jasonsbeer/AmigaPCI/DataSheets/TimingDiagrams/Bus Sizing/ALTERNATING RW BYTE TRANSFER TO LONG WORD PORT.png

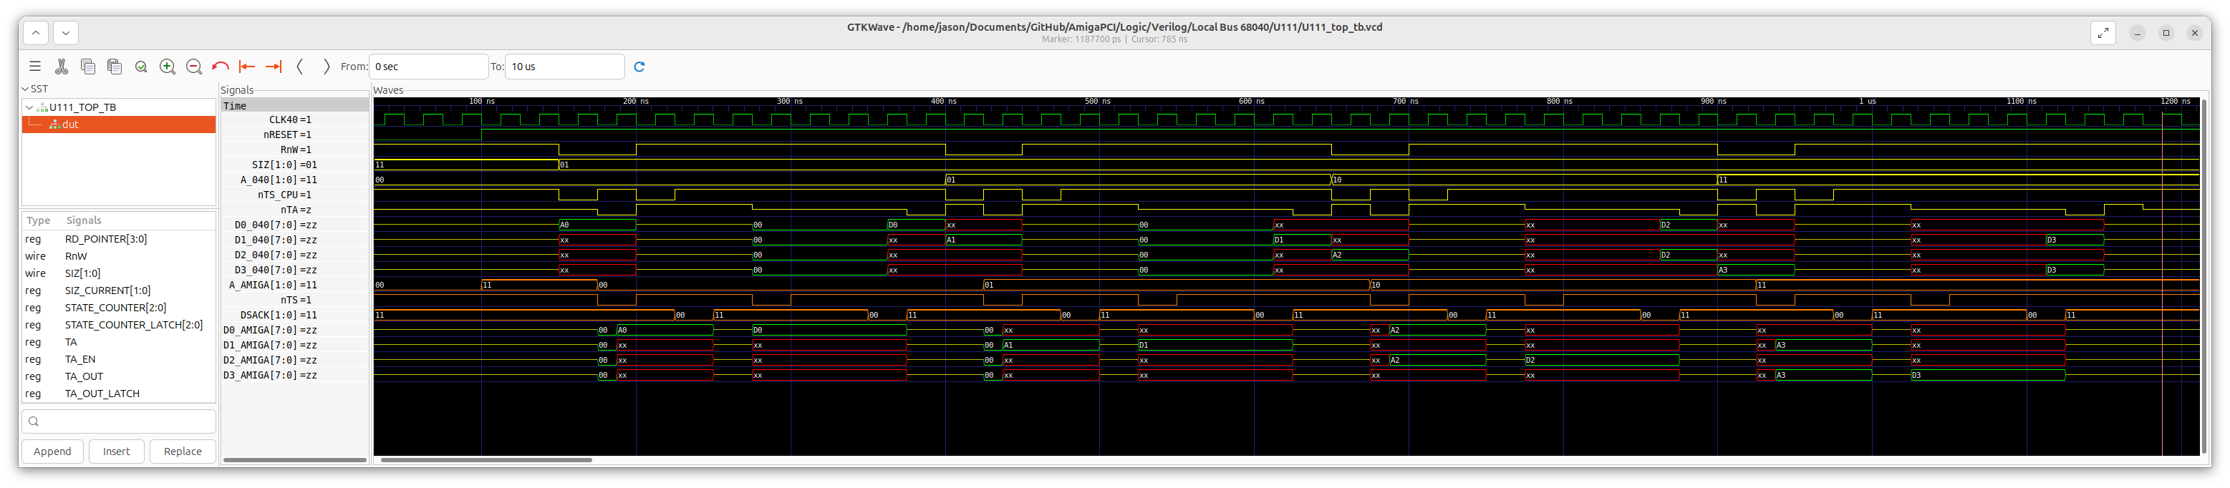
DataSheets/TimingDiagrams/Bus Sizing/ALTERNATING RW BYTE TRANSFER TO LONG WORD PORT.png
