jasonsbeer/AmigaPCI/DataSheets/TimingDiagrams/Bus Sizing/ALTERNATING RW BYTE TRANSFER TO WORD PORT.png

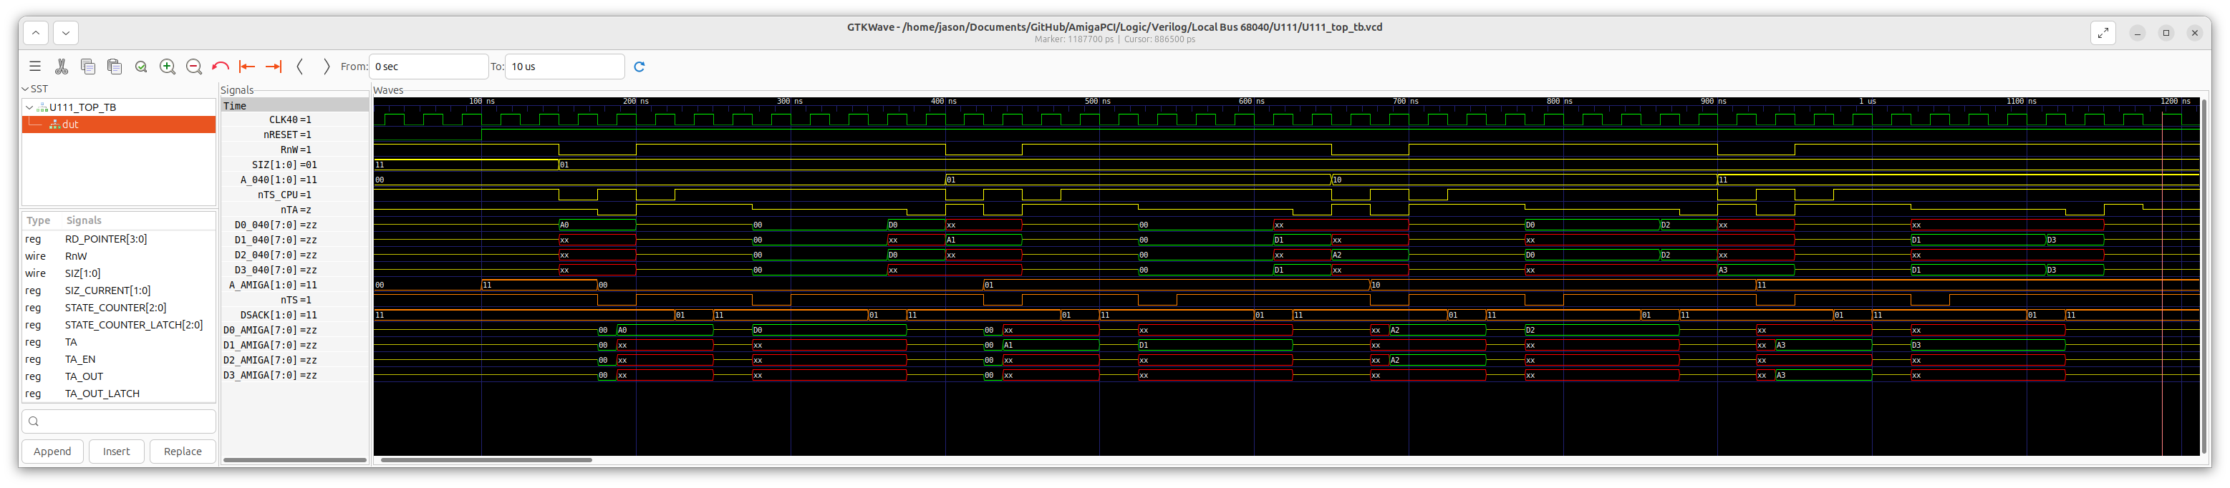
DataSheets/TimingDiagrams/Bus Sizing/ALTERNATING RW BYTE TRANSFER TO WORD PORT.png
