jasonsbeer/AmigaPCI/DataSheets/TimingDiagrams/Bus Sizing/ALTERNATING RW LINE TRANSFER TO LONG WORD PORT WITH WAITS.png

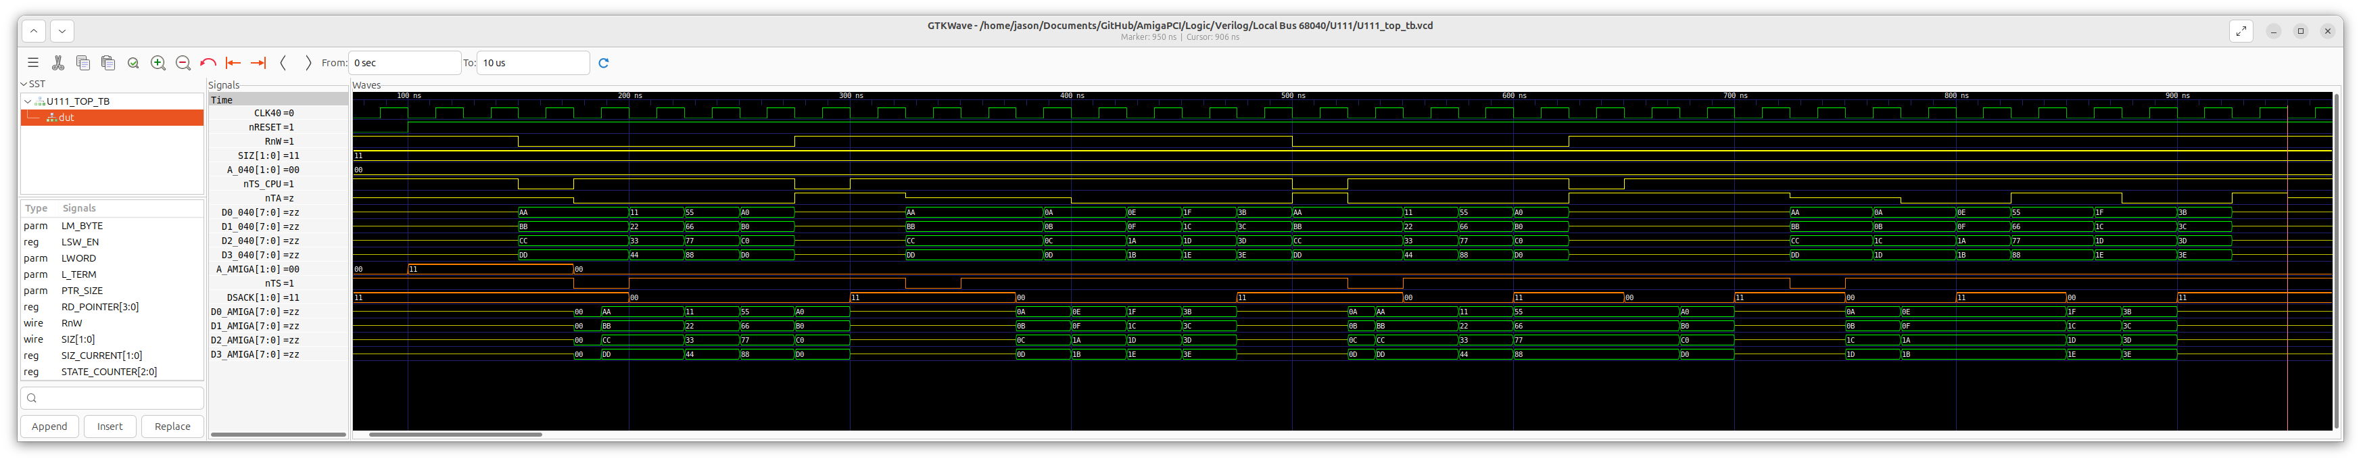
DataSheets/TimingDiagrams/Bus Sizing/ALTERNATING RW LINE TRANSFER TO LONG WORD PORT WITH WAITS.png
