jasonsbeer/AmigaPCI/DataSheets/TimingDiagrams/Bus Sizing/ALTERNATING RW LINE TRANSFER TO WORD PORT.png

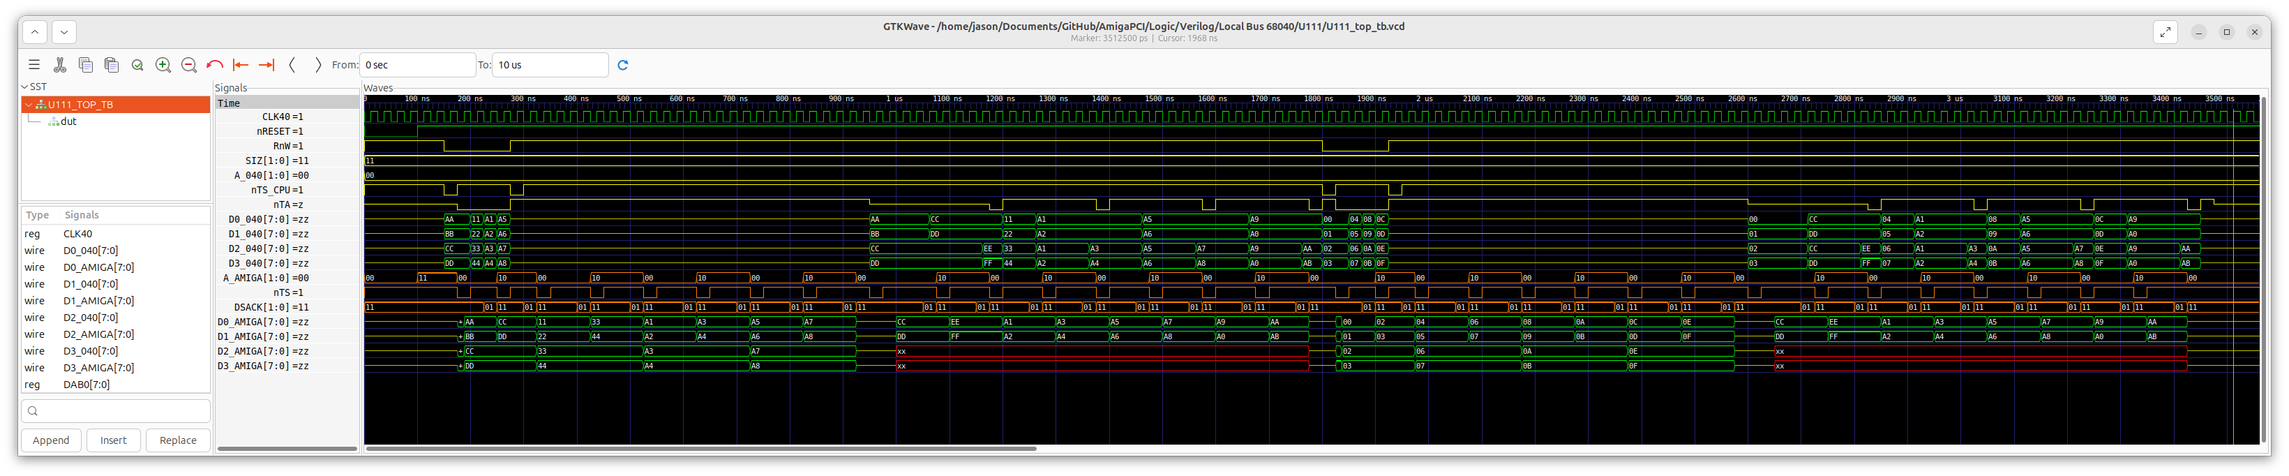
DataSheets/TimingDiagrams/Bus Sizing/ALTERNATING RW LINE TRANSFER TO WORD PORT.png
