jasonsbeer/AmigaPCI/DataSheets/TimingDiagrams/Bus Sizing/ALTERNATING RW LONG WORD TO WORD PORT.png

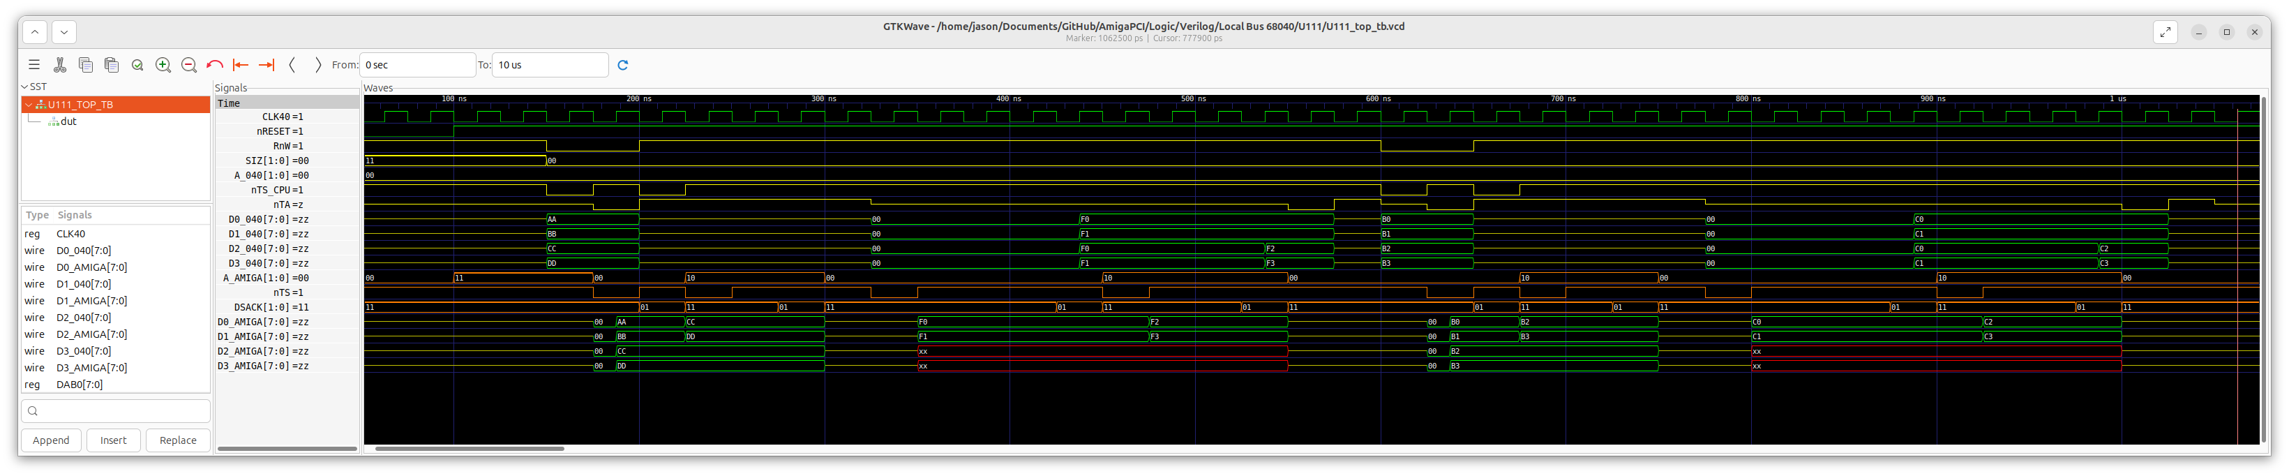
DataSheets/TimingDiagrams/Bus Sizing/ALTERNATING RW LONG WORD TO WORD PORT.png
