jasonsbeer/AmigaPCI/DataSheets/TimingDiagrams/Bus Sizing/ALTERNATING RW WORD TO LONG WORD PORT.png

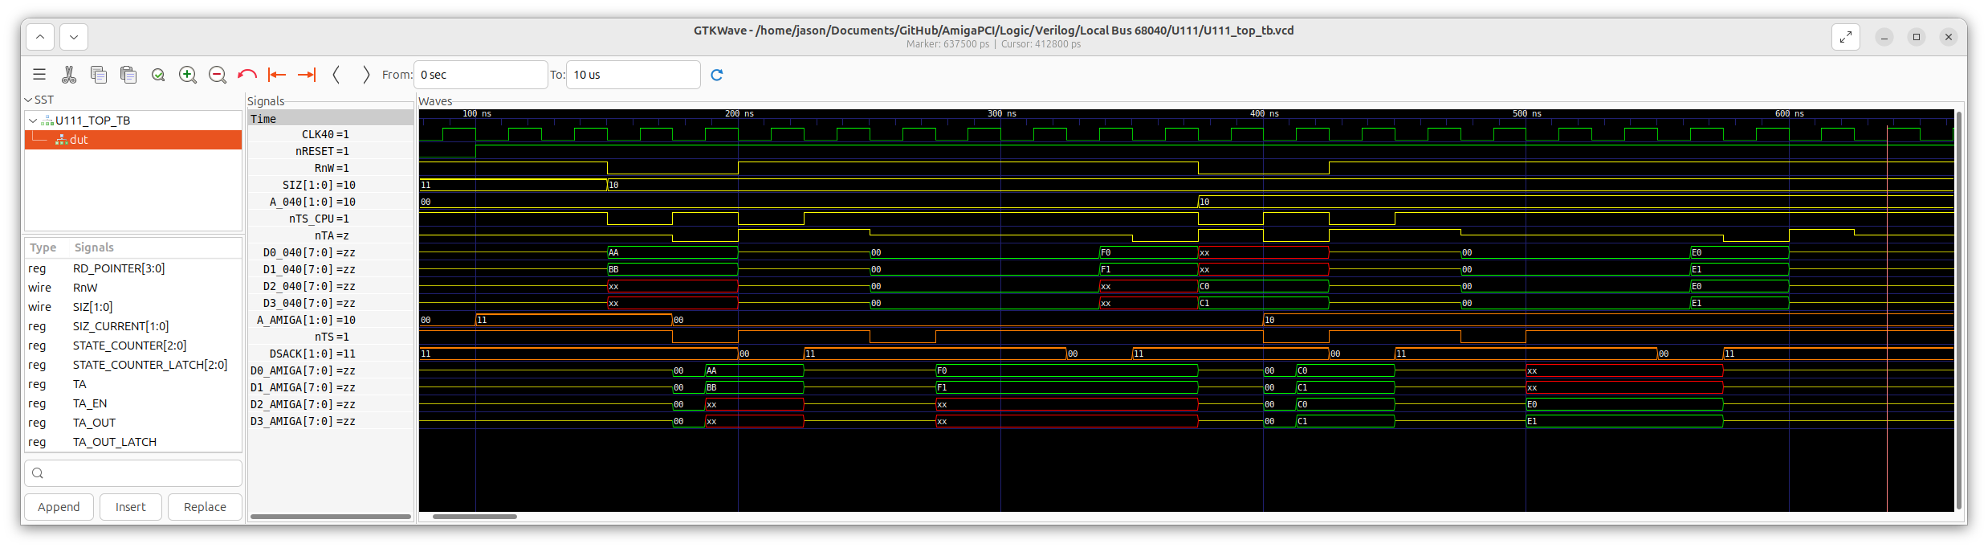
DataSheets/TimingDiagrams/Bus Sizing/ALTERNATING RW WORD TO LONG WORD PORT.png
