jasonsbeer/AmigaPCI/DataSheets/TimingDiagrams/Bus Sizing/BYTE READ FROM LONG WORD PORT.png

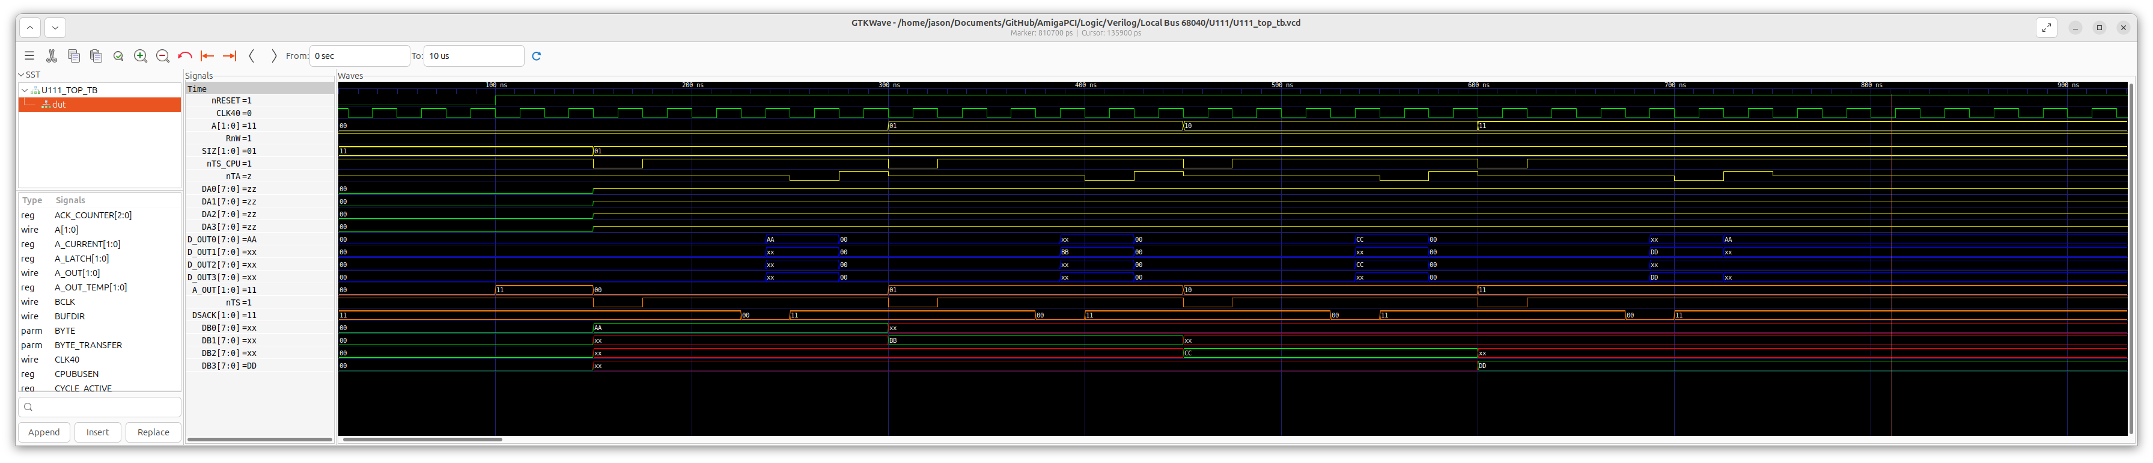
DataSheets/TimingDiagrams/Bus Sizing/BYTE READ FROM LONG WORD PORT.png
