jasonsbeer/AmigaPCI/DataSheets/TimingDiagrams/Bus Sizing/BYTE READ FROM WORD PORT.png

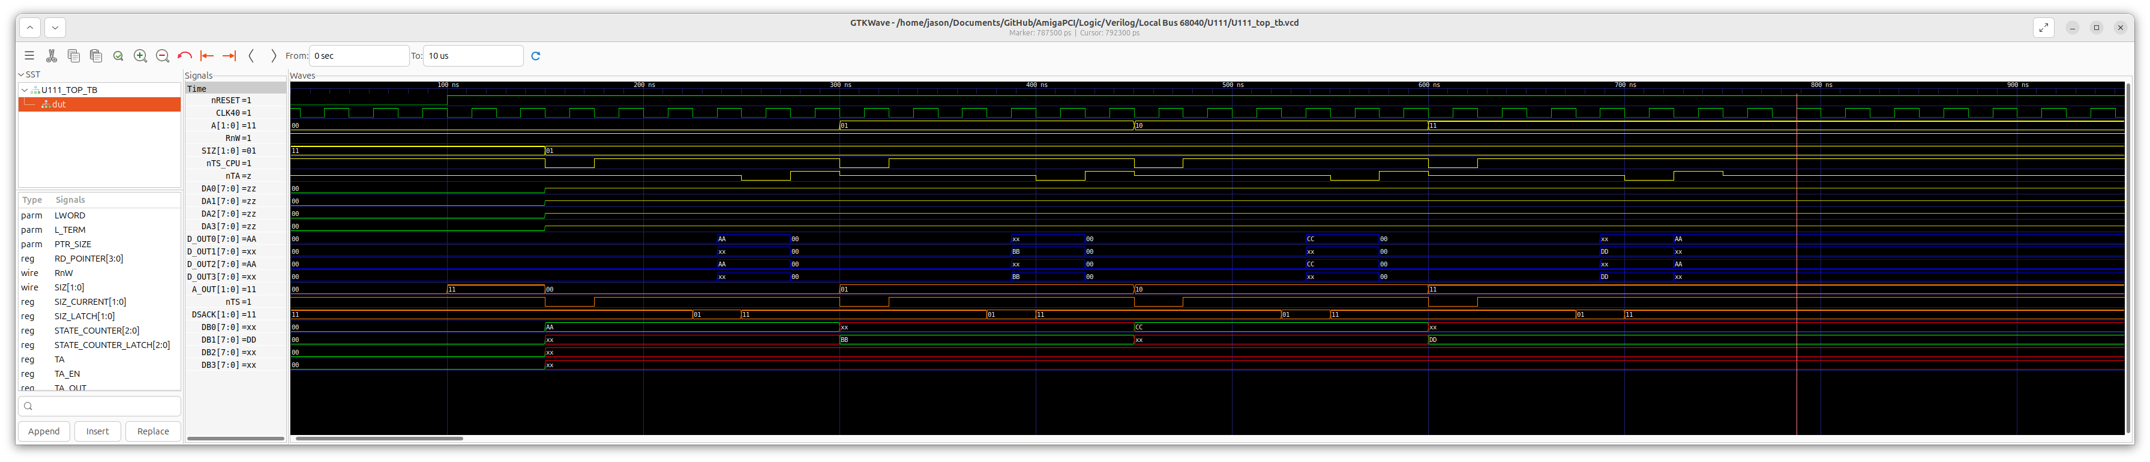
DataSheets/TimingDiagrams/Bus Sizing/BYTE READ FROM WORD PORT.png
