jasonsbeer/AmigaPCI/DataSheets/TimingDiagrams/Bus Sizing/BYTE WRITE TO LONG WORD PORT.png

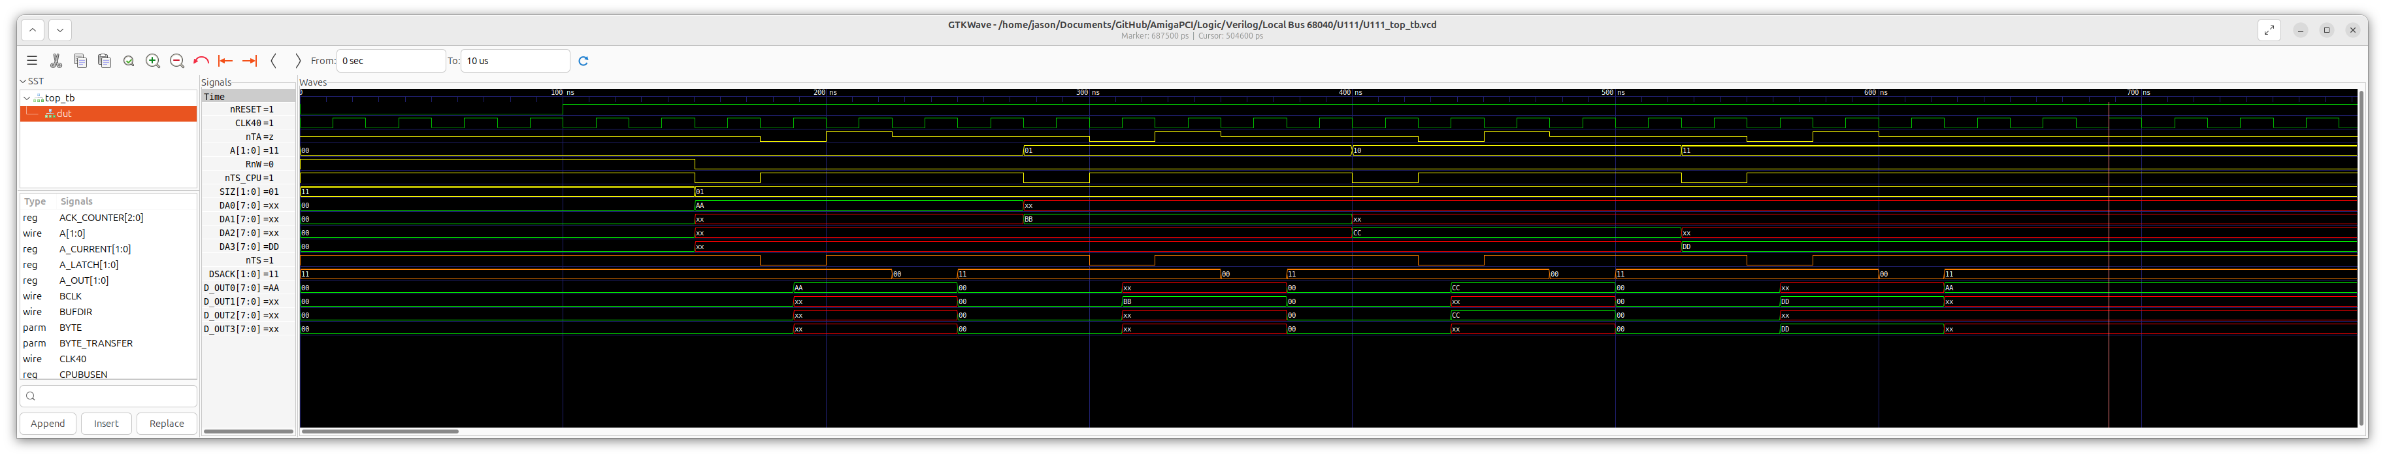
DataSheets/TimingDiagrams/Bus Sizing/BYTE WRITE TO LONG WORD PORT.png
