jasonsbeer/AmigaPCI/DataSheets/TimingDiagrams/Bus Sizing/LINE READ FROM A WORD PORT.png

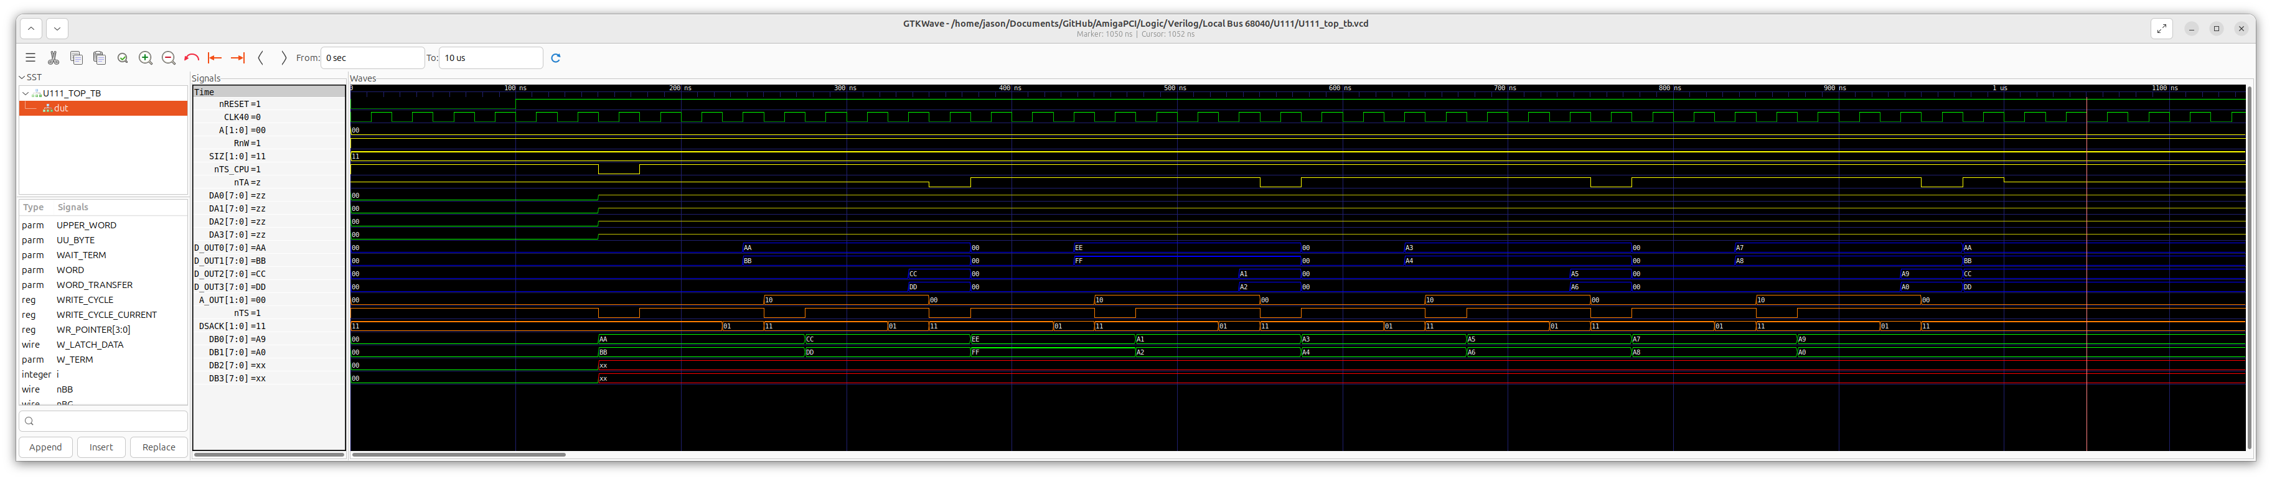
DataSheets/TimingDiagrams/Bus Sizing/LINE READ FROM A WORD PORT.png
