jasonsbeer/AmigaPCI/DataSheets/TimingDiagrams/Bus Sizing/LINE READ FROM LONG WORD PORT.png

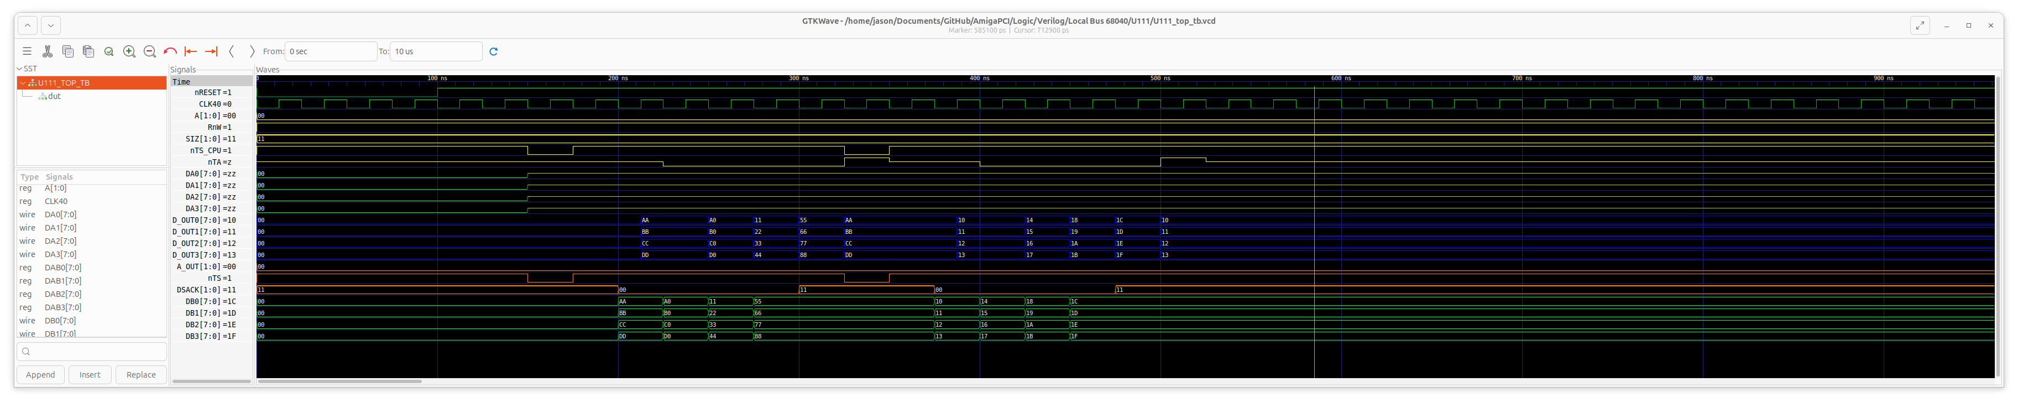
DataSheets/TimingDiagrams/Bus Sizing/LINE READ FROM LONG WORD PORT.png
