jasonsbeer/AmigaPCI/DataSheets/TimingDiagrams/Bus Sizing/LINE WRITE TO LONG WORD PORT.png

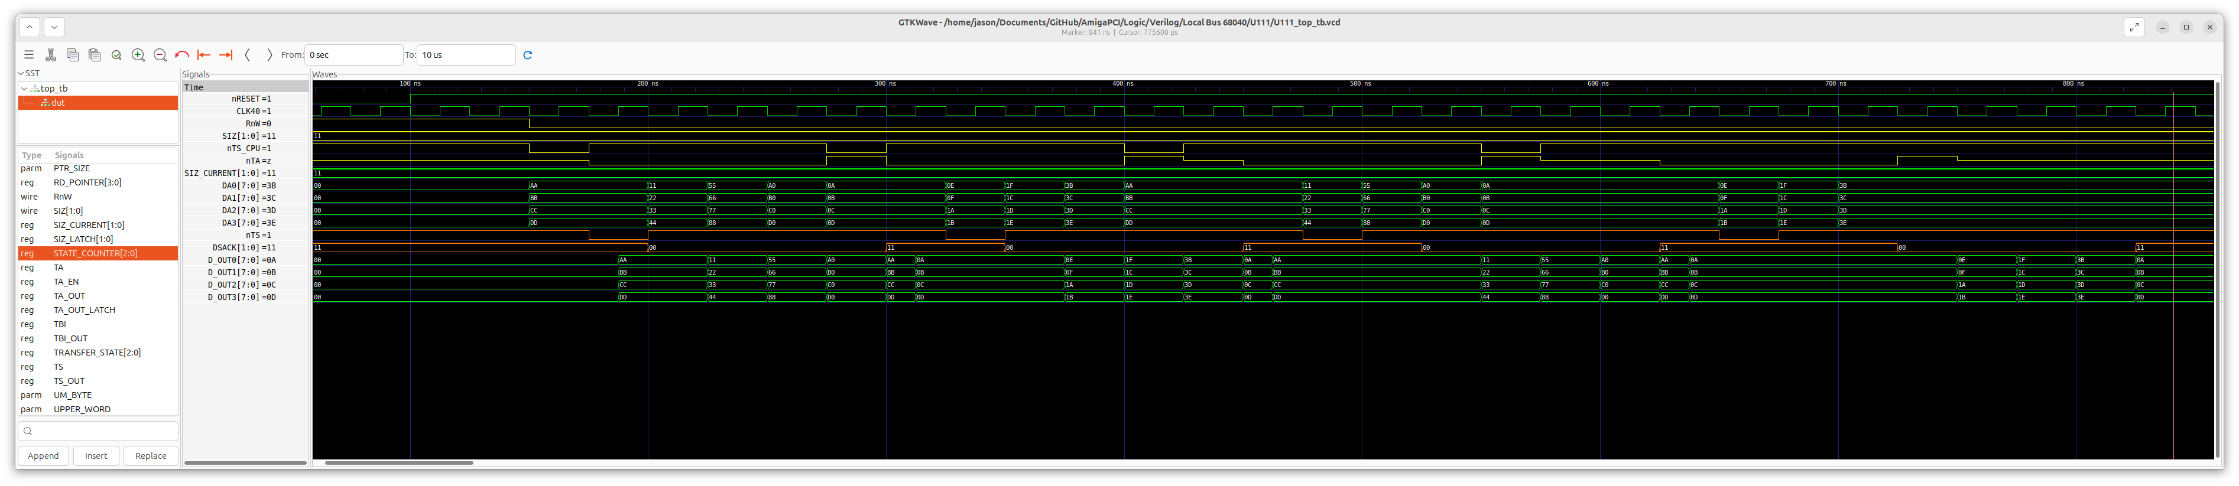
DataSheets/TimingDiagrams/Bus Sizing/LINE WRITE TO LONG WORD PORT.png
