jasonsbeer/AmigaPCI/DataSheets/TimingDiagrams/Bus Sizing/LINE WRITE TO WORD PORT.png

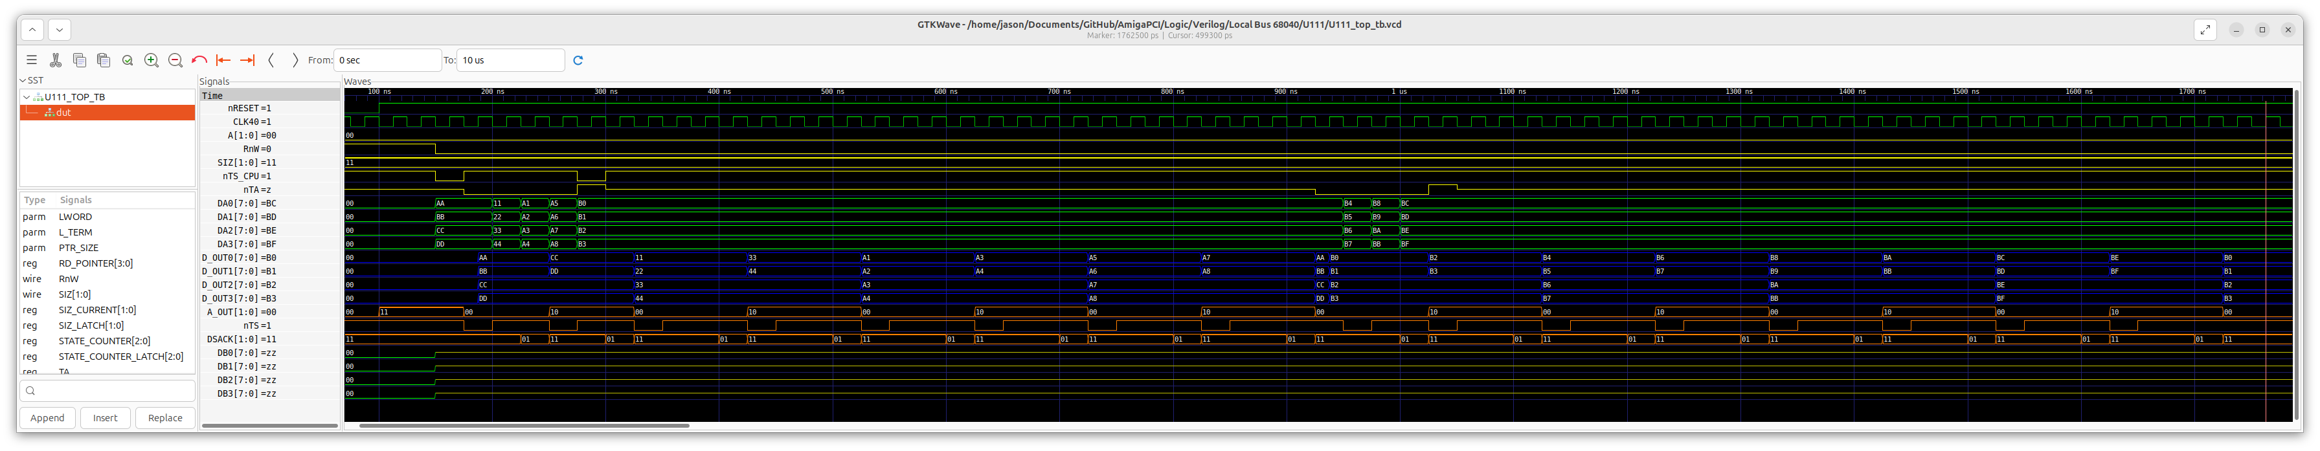
DataSheets/TimingDiagrams/Bus Sizing/LINE WRITE TO WORD PORT.png
