jasonsbeer/AmigaPCI/DataSheets/TimingDiagrams/Bus Sizing/LONG WORD READ FROM LONG WORD PORT.png

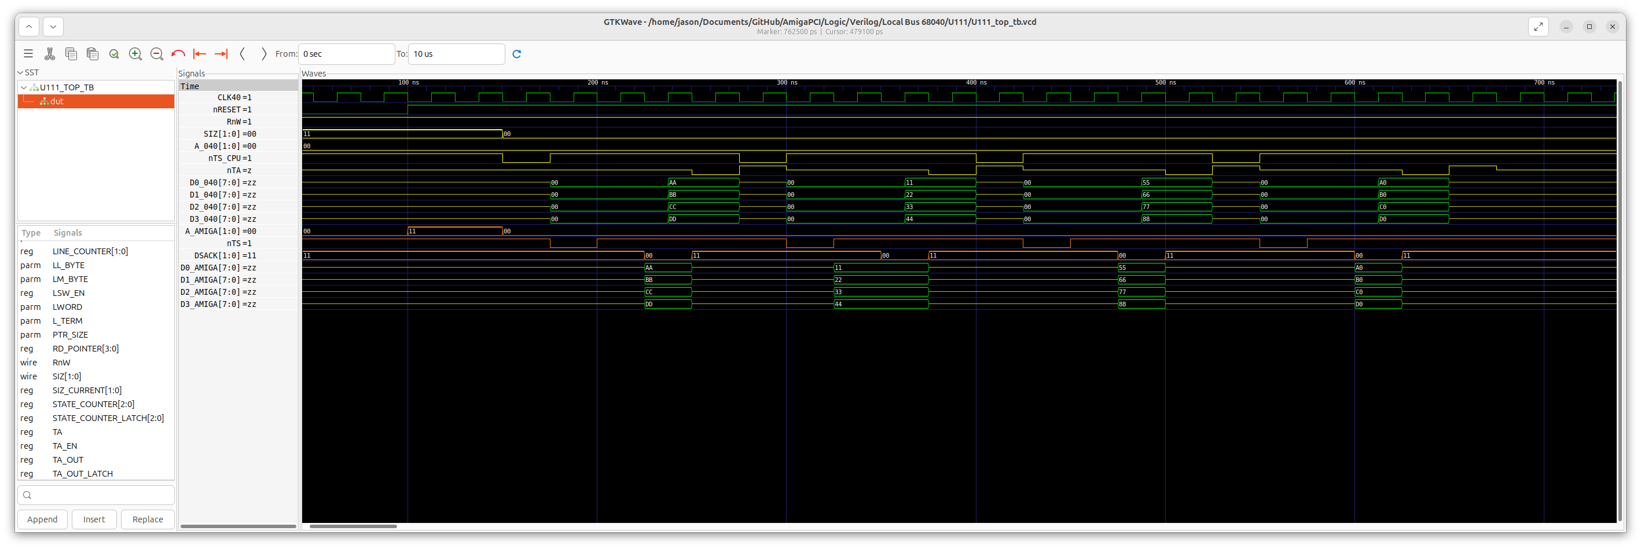
DataSheets/TimingDiagrams/Bus Sizing/LONG WORD READ FROM LONG WORD PORT.png
