jasonsbeer/AmigaPCI/DataSheets/TimingDiagrams/Bus Sizing/LONG WORD WRITE TO WORD PORT.png

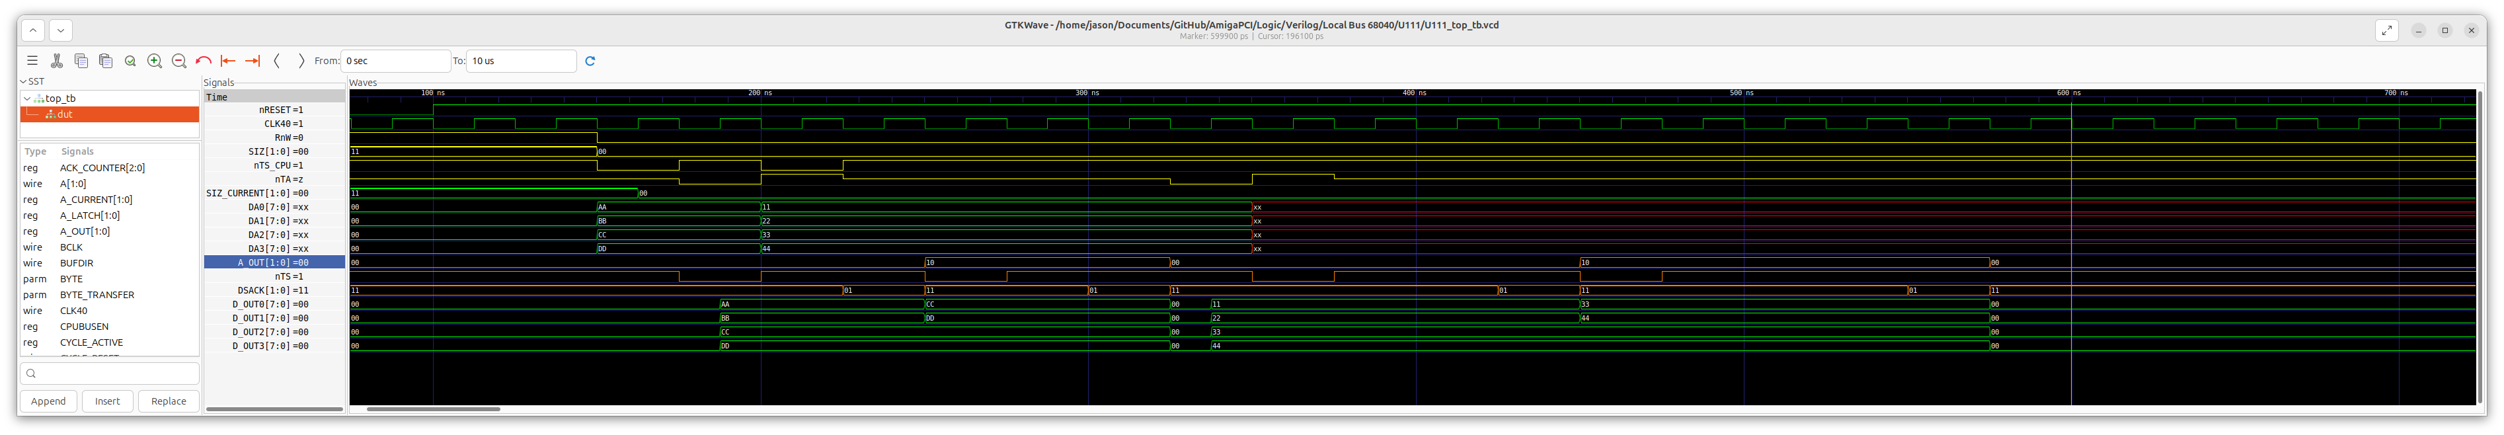
DataSheets/TimingDiagrams/Bus Sizing/LONG WORD WRITE TO WORD PORT.png
