jasonsbeer/AmigaPCI/DataSheets/TimingDiagrams/Bus Sizing/WORD READ FROM WORD PORT.png

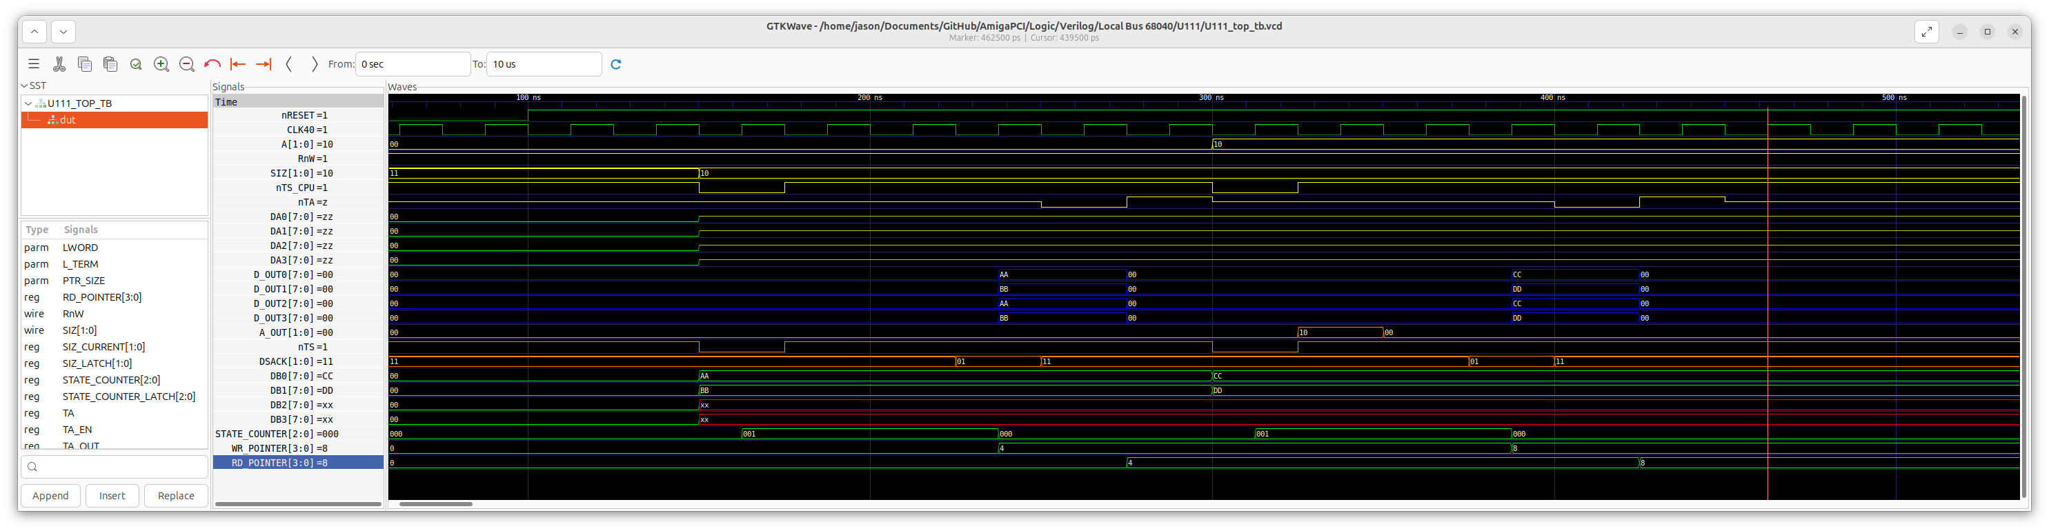
DataSheets/TimingDiagrams/Bus Sizing/WORD READ FROM WORD PORT.png
