jasonsbeer/AmigaPCI/DataSheets/TimingDiagrams/CHIP RAM CPU AND DMA READ CYCLES.png

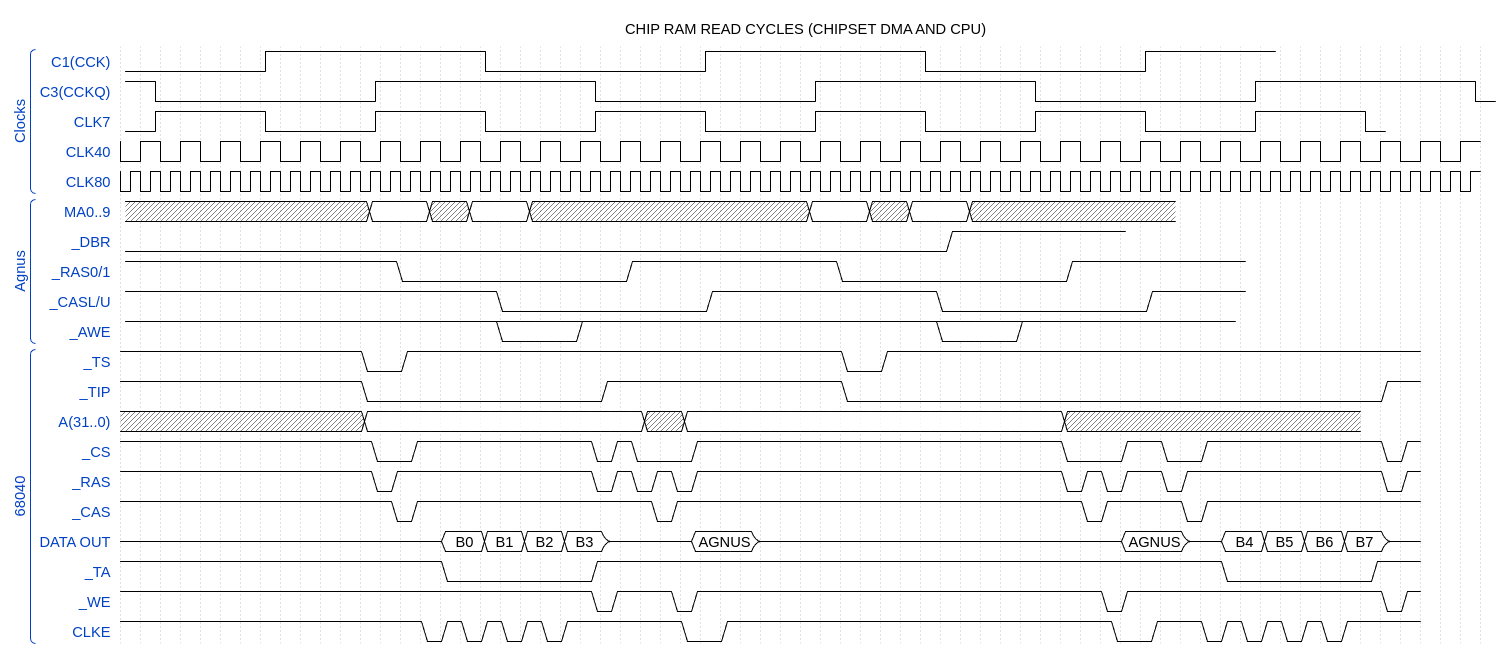
DataSheets/TimingDiagrams/CHIP RAM CPU AND DMA READ CYCLES.png
