jasonsbeer/AmigaPCI/DataSheets/TimingDiagrams/CIA Cycle Best Case Read.png

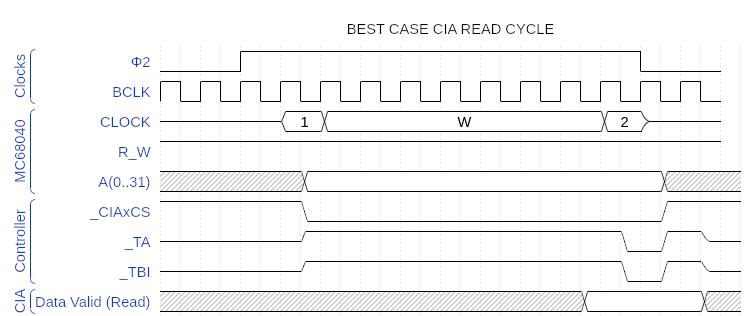
DataSheets/TimingDiagrams/CIA Cycle Best Case Read.png
