jasonsbeer/AmigaPCI/DataSheets/TimingDiagrams/CIA Cycle Best Case Write.png

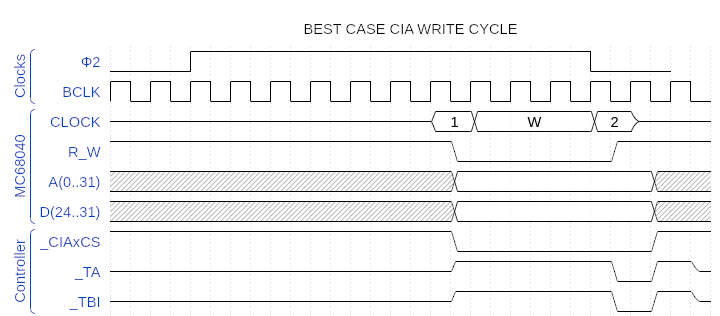
DataSheets/TimingDiagrams/CIA Cycle Best Case Write.png
