jasonsbeer/AmigaPCI/DataSheets/TimingDiagrams/CIA Cycle Worst Case Read.png

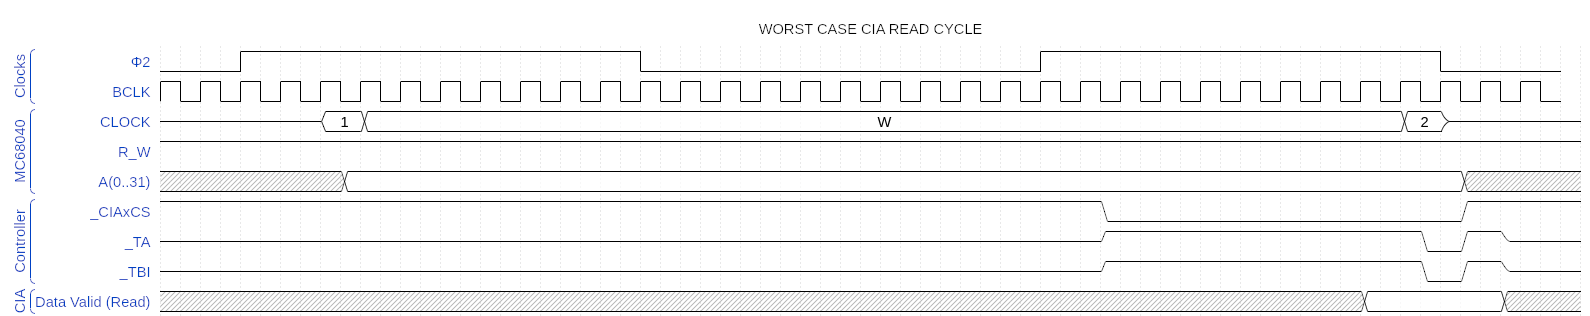
DataSheets/TimingDiagrams/CIA Cycle Worst Case Read.png
