jasonsbeer/AmigaPCI/DataSheets/TimingDiagrams/CIA Cycle Worst Case Write.png

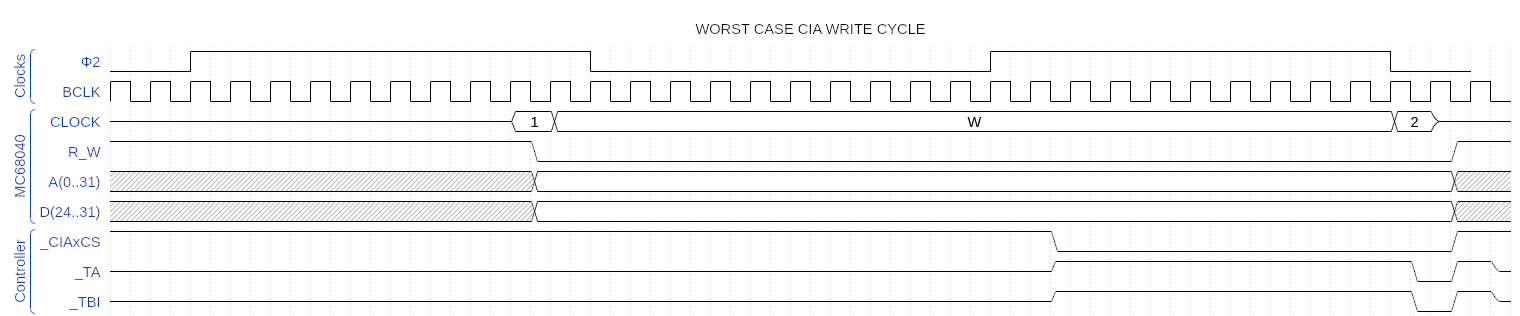
DataSheets/TimingDiagrams/CIA Cycle Worst Case Write.png
