jasonsbeer/AmigaPCI/DataSheets/TimingDiagrams/CPU Chipset RAM Cycle.png

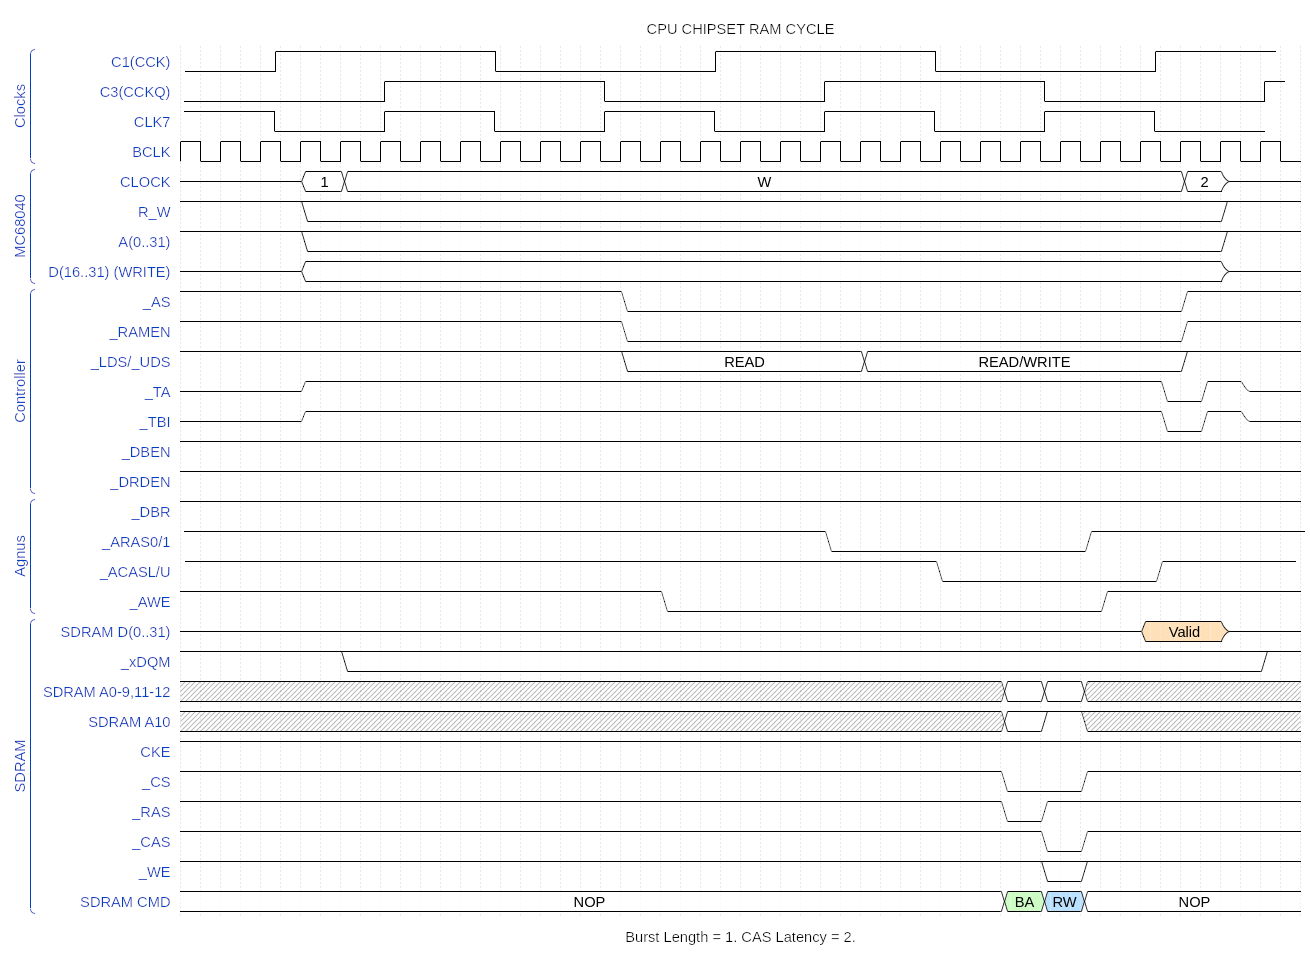
DataSheets/TimingDiagrams/CPU Chipset RAM Cycle.png
