jasonsbeer/AmigaPCI/DataSheets/TimingDiagrams/CPU Driven Burst Read Cycle Fast With PCI Wait.png

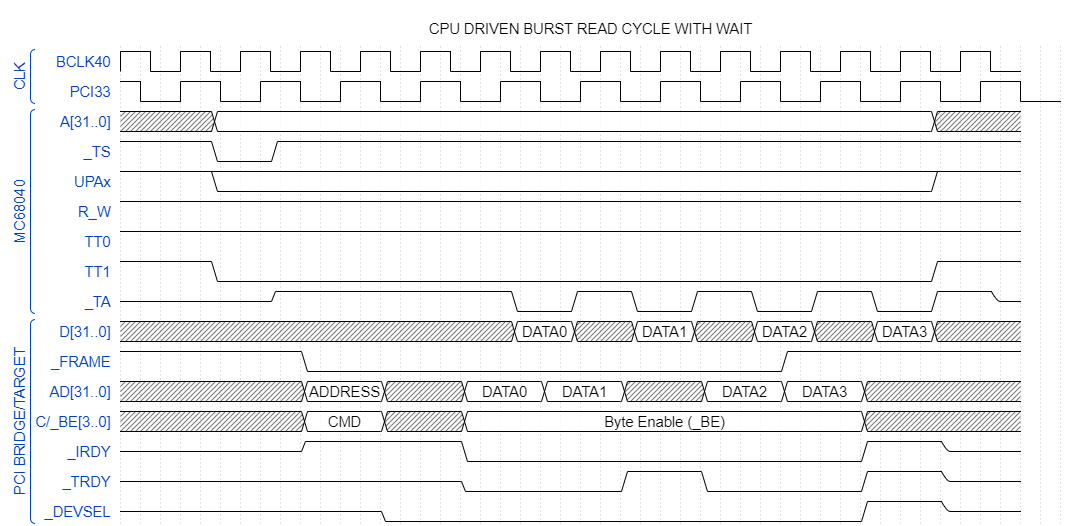
DataSheets/TimingDiagrams/CPU Driven Burst Read Cycle Fast With PCI Wait.png
