jasonsbeer/AmigaPCI/DataSheets/TimingDiagrams/CPU Driven Burst Read Cycle Fast.png

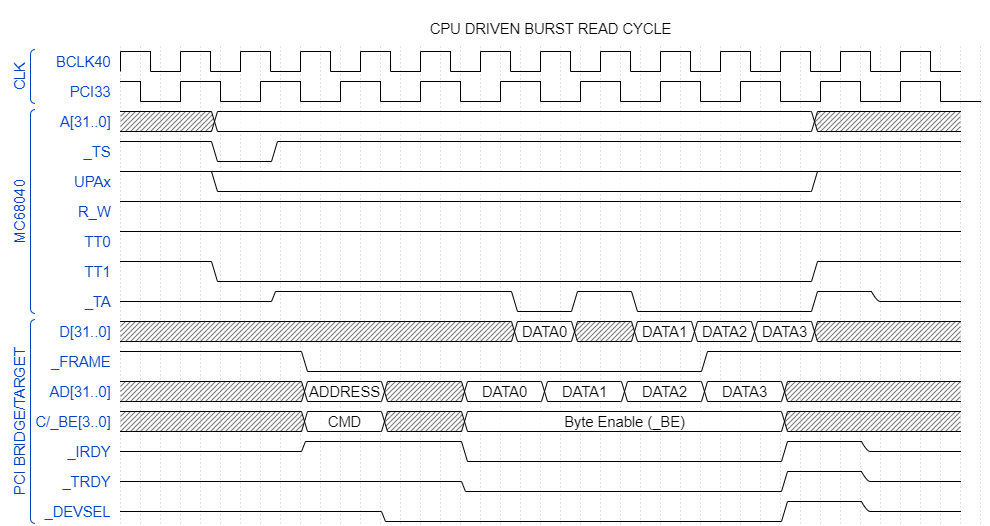
DataSheets/TimingDiagrams/CPU Driven Burst Read Cycle Fast.png
