jasonsbeer/AmigaPCI/DataSheets/TimingDiagrams/Fast RAM.png

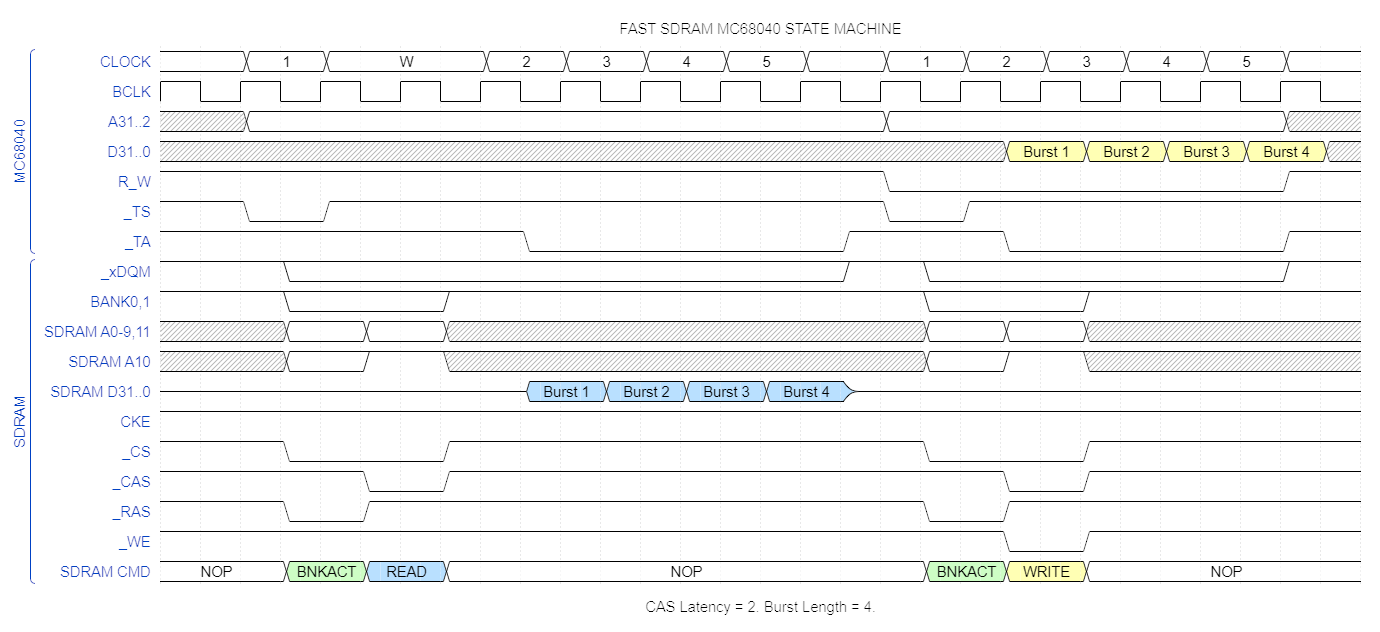
DataSheets/TimingDiagrams/Fast RAM.png
