jasonsbeer/AmigaPCI/DataSheets/TimingDiagrams/PCI Burst Cycle Disconnect.png

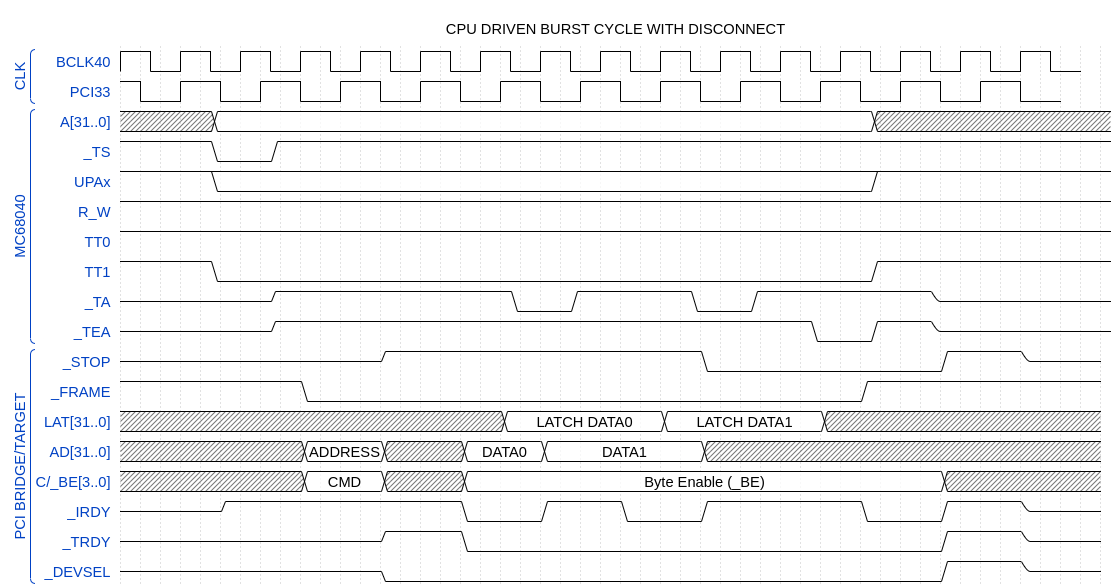
DataSheets/TimingDiagrams/PCI Burst Cycle Disconnect.png
