jasonsbeer/AmigaPCI/DataSheets/TimingDiagrams/PCI Burst Write Cycle Fast.png

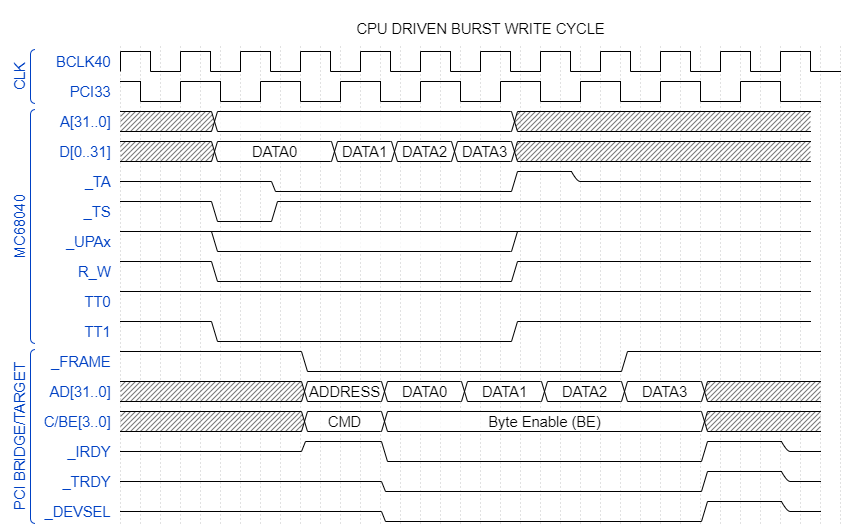
DataSheets/TimingDiagrams/PCI Burst Write Cycle Fast.png
