jasonsbeer/AmigaPCI/DataSheets/TimingDiagrams/PCI Burst Write Cycle Wait Fast.png

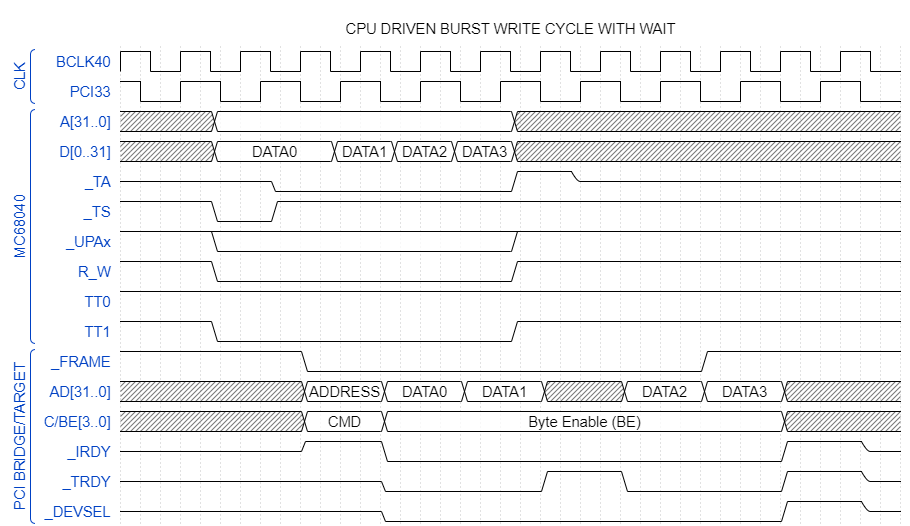
DataSheets/TimingDiagrams/PCI Burst Write Cycle Wait Fast.png
