jasonsbeer/AmigaPCI/DataSheets/TimingDiagrams/PCI Burst Write Cycle Wait.png

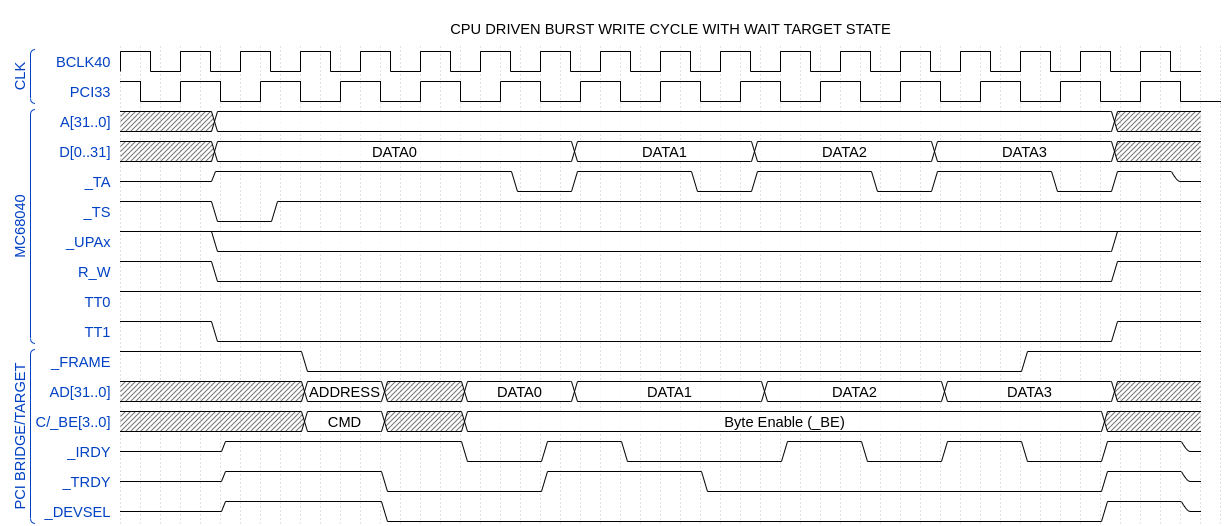
DataSheets/TimingDiagrams/PCI Burst Write Cycle Wait.png
