jasonsbeer/AmigaPCI/DataSheets/TimingDiagrams/PCI Burst Write Cycle.png

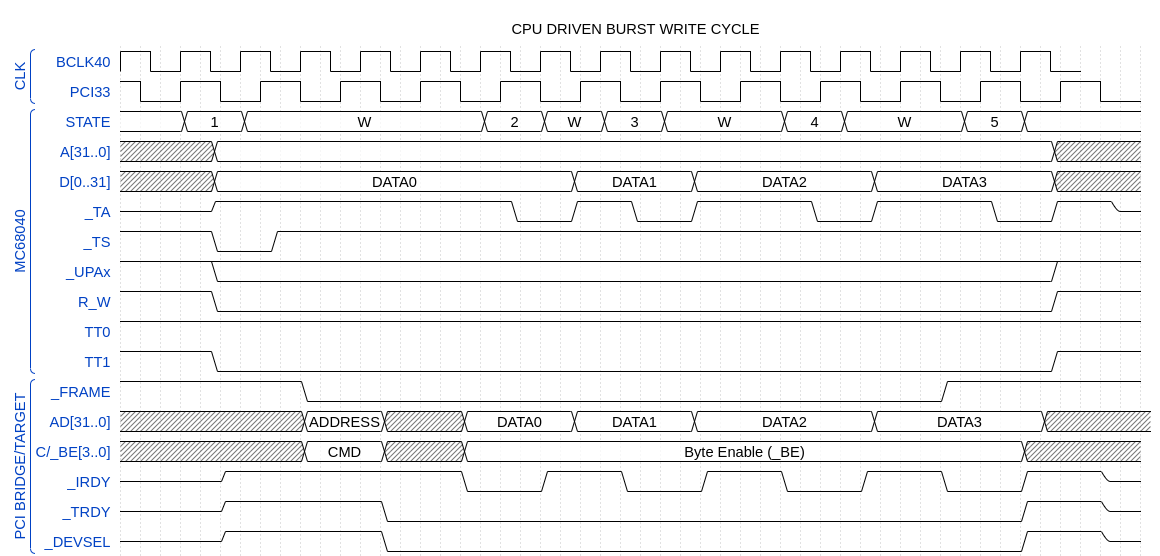
DataSheets/TimingDiagrams/PCI Burst Write Cycle.png
