jasonsbeer/AmigaPCI/DataSheets/TimingDiagrams/PCI Configuration Read Cycle.png

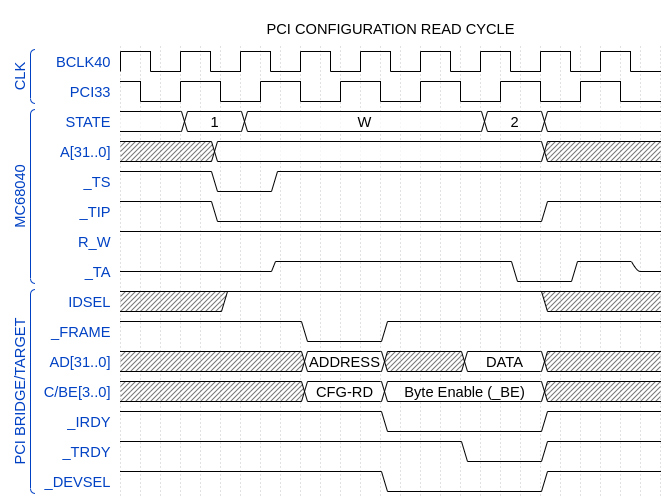
DataSheets/TimingDiagrams/PCI Configuration Read Cycle.png
