jasonsbeer/AmigaPCI/DataSheets/TimingDiagrams/PCI Configuration Write Cycle.png

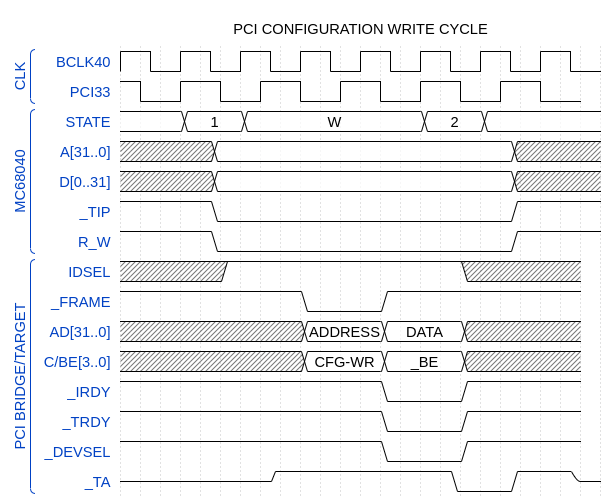
DataSheets/TimingDiagrams/PCI Configuration Write Cycle.png
