jasonsbeer/AmigaPCI/DataSheets/TimingDiagrams/PCI Cycle Retry.png

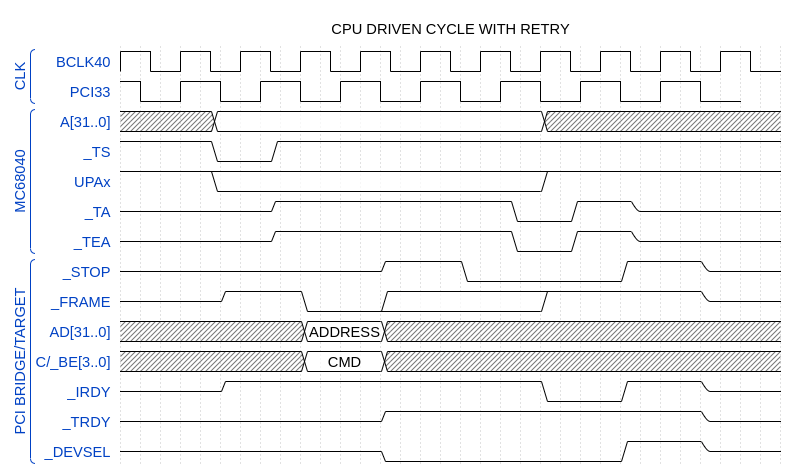
DataSheets/TimingDiagrams/PCI Cycle Retry.png
