jasonsbeer/AmigaPCI/DataSheets/TimingDiagrams/PCI DMA Burst Read Cycle With Wait.png

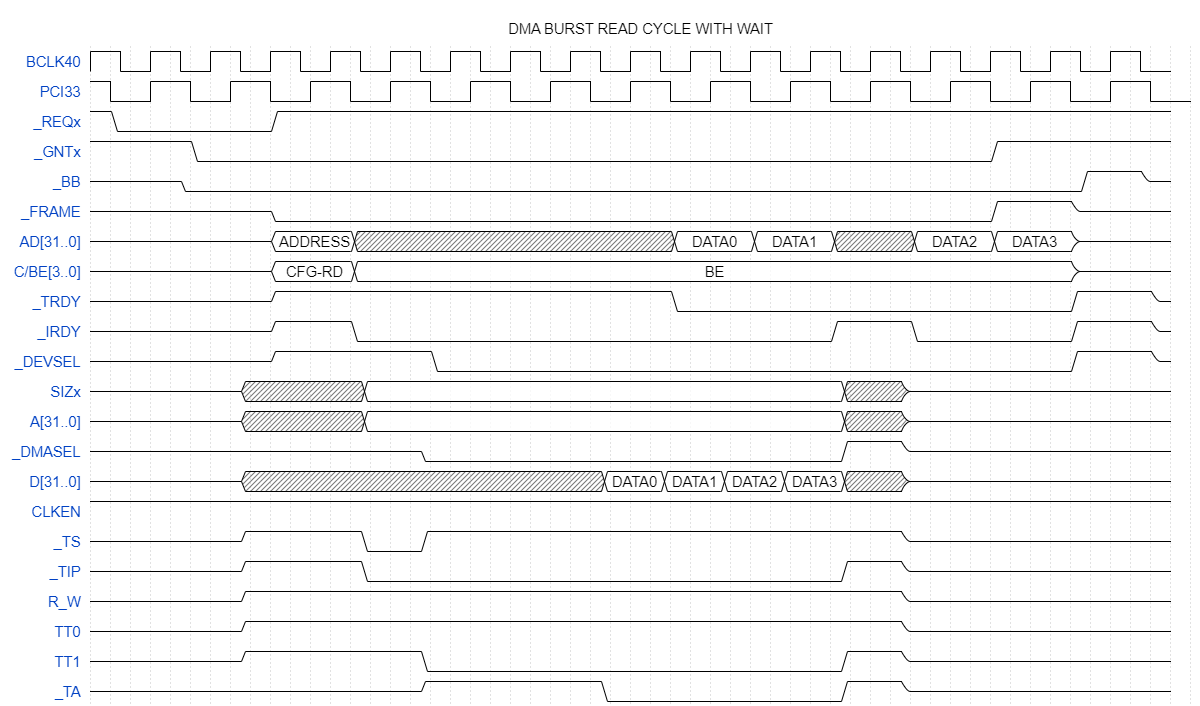
DataSheets/TimingDiagrams/PCI DMA Burst Read Cycle With Wait.png
