jasonsbeer/AmigaPCI/DataSheets/TimingDiagrams/PCI DMA Burst Read Cycle.png

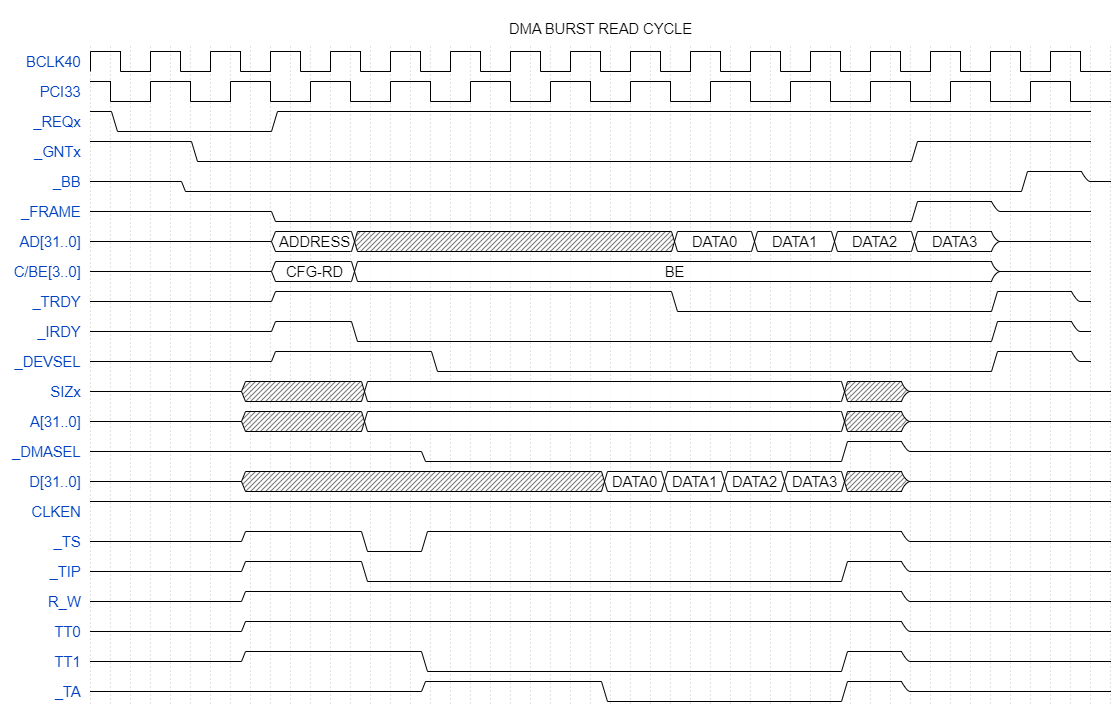
DataSheets/TimingDiagrams/PCI DMA Burst Read Cycle.png
