jasonsbeer/AmigaPCI/DataSheets/TimingDiagrams/PCI DMA Burst Write Cycle With Wait.png

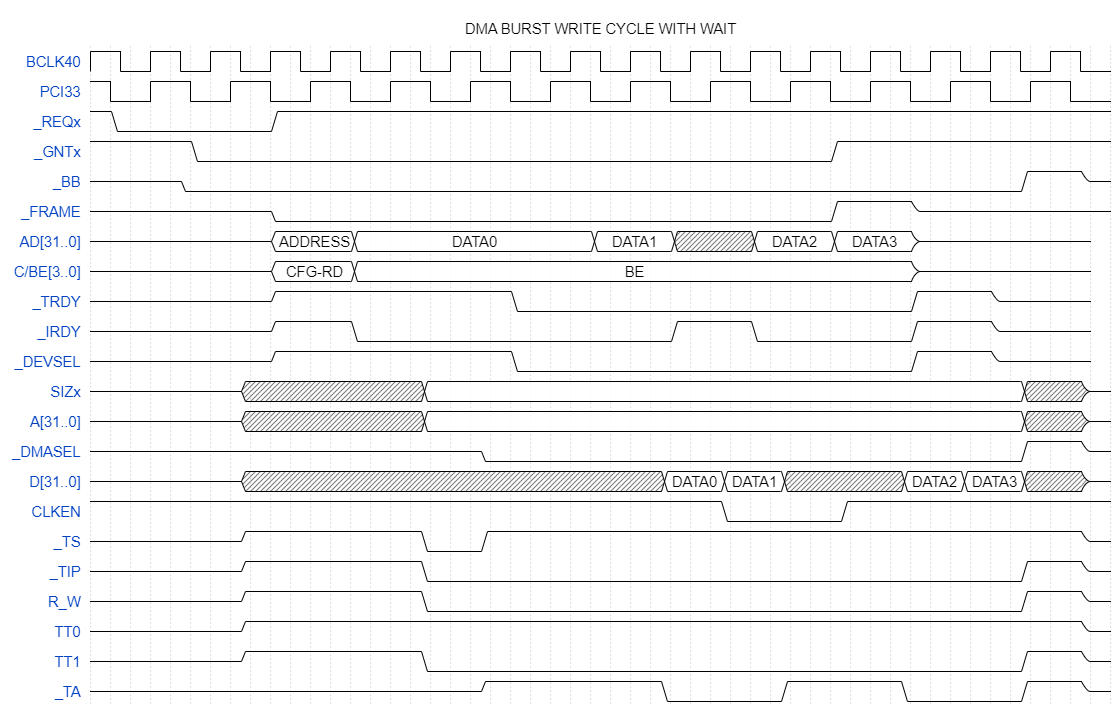
DataSheets/TimingDiagrams/PCI DMA Burst Write Cycle With Wait.png
