jasonsbeer/AmigaPCI/DataSheets/TimingDiagrams/PCI DMA Burst Write Cycle.png

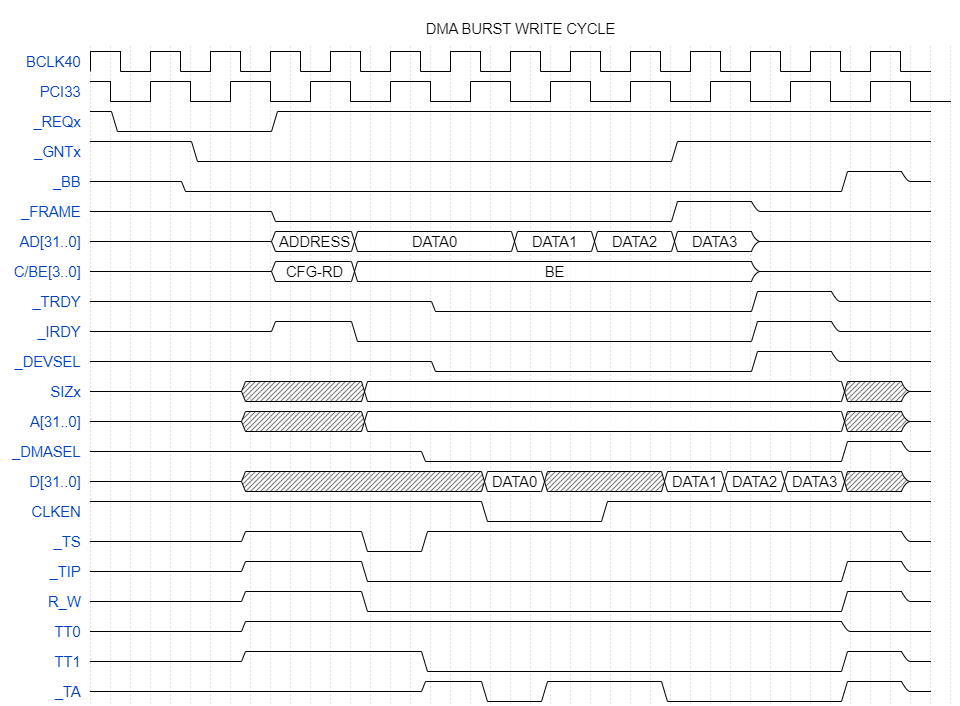
DataSheets/TimingDiagrams/PCI DMA Burst Write Cycle.png
