jasonsbeer/AmigaPCI/DataSheets/TimingDiagrams/PCI DMA Normal Read Cycle.png

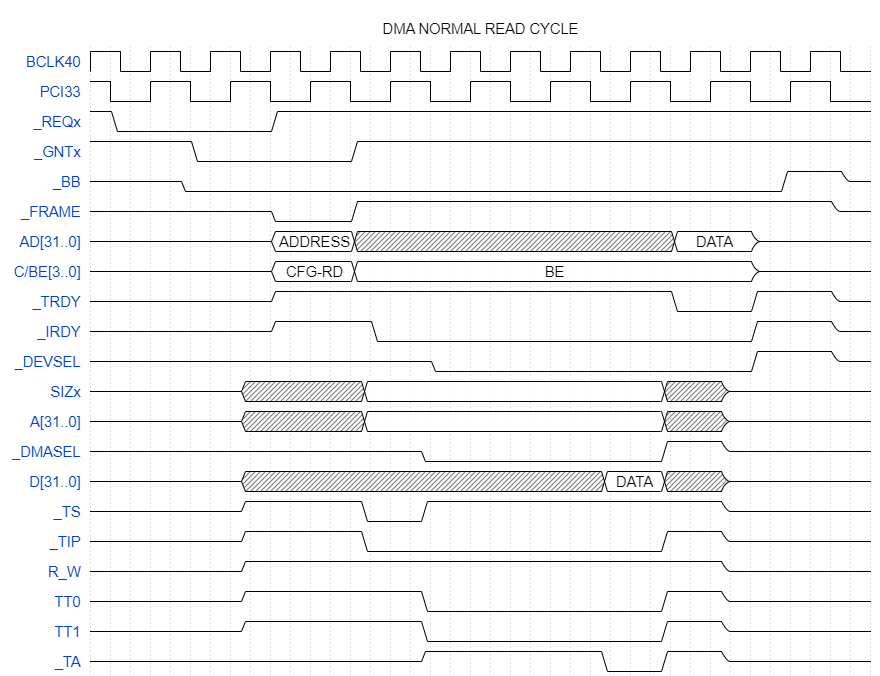
DataSheets/TimingDiagrams/PCI DMA Normal Read Cycle.png
