jasonsbeer/AmigaPCI/DataSheets/TimingDiagrams/PCI DMA Normal Write Cycle.png

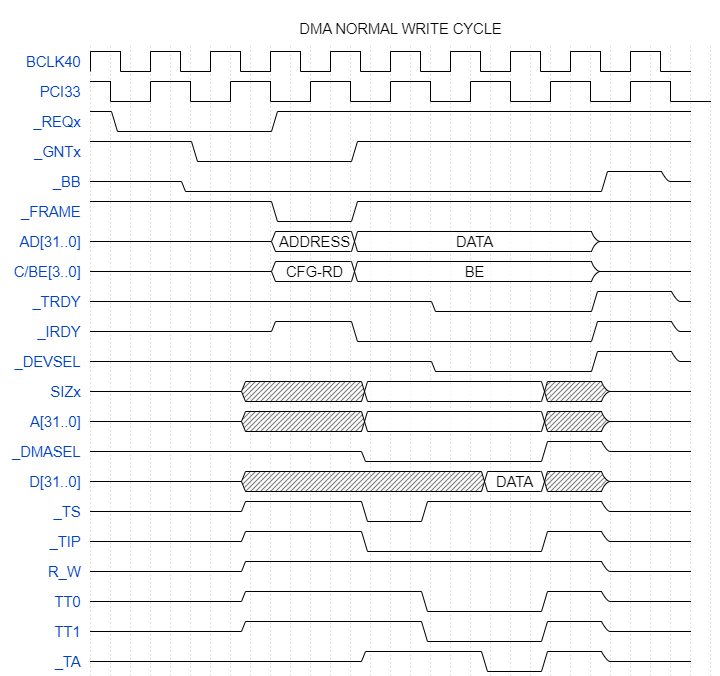
DataSheets/TimingDiagrams/PCI DMA Normal Write Cycle.png
