jasonsbeer/AmigaPCI/DataSheets/TimingDiagrams/PCI Normal Read Cycle.png

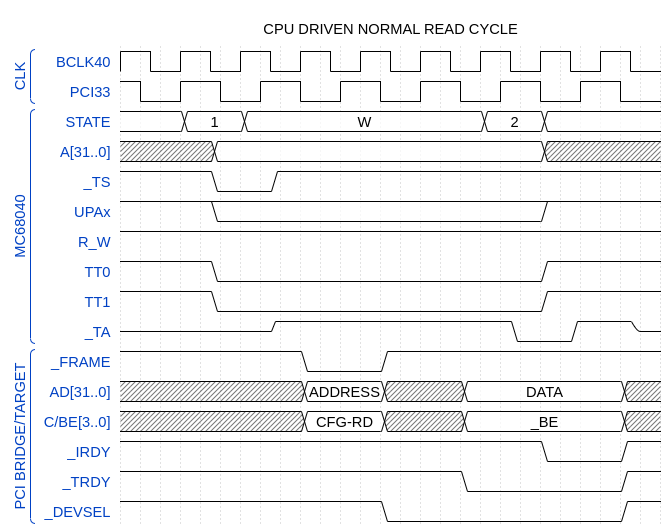
DataSheets/TimingDiagrams/PCI Normal Read Cycle.png
