jasonsbeer/AmigaPCI/DataSheets/TimingDiagrams/PCI Normal Write Cycle.png

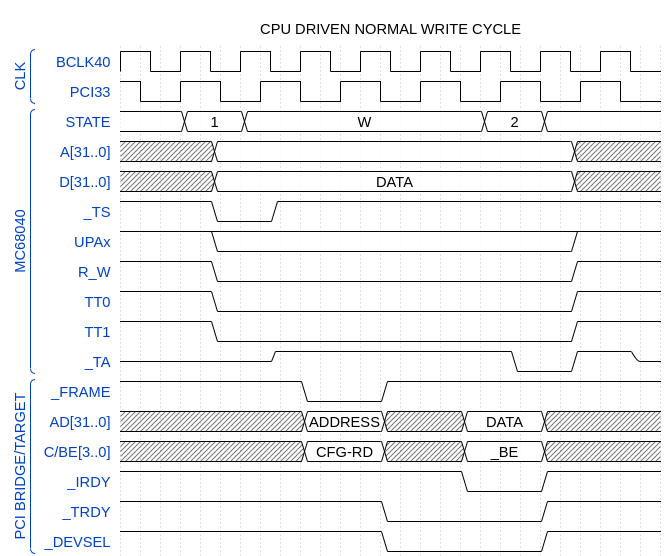
DataSheets/TimingDiagrams/PCI Normal Write Cycle.png
