jasonsbeer/AmigaPCI/Logic/Verilog/AmigaPCI/U712/U712_CHIPSET_RAM.v

/*
LICENSE:

This work is released under the Creative Commons Attribution-NonCommercial 4.0 International
https://creativecommons.org/licenses/by-nc/4.0/

You are free to:
Share — copy and redistribute the material in any medium or format
Adapt — remix, transform, and build upon the material
The licensor cannot revoke these freedoms as long as you follow the license terms.

Under the following terms:
Attribution — You must give appropriate credit , provide a link to the license, and indicate if changes were made . You may do so in any reasonable manner, but not in any way that suggests the licensor endorses you or your use.
NonCommercial — You may not use the material for commercial purposes.
No additional restrictions — You may not apply legal terms or technological measures that legally restrict others from doing anything the license permits.

RTL MODULE:

Engineer: Jason Neus
Design Name: U712
Module Name: U712_CHIPSET_RAM
Project Name: AmigaPCI
Target Devices: iCE40-HX4K-TQ144

Description: CHIP RAM CYCLES

Revision History:
    16-JUN-2024 : INITIAL RELEASE
    17-JUN-2024 : SET BRIDGE ENABLE WITH COLUMN MA0 (A1)
    19-JUN-2024 : ALIGNED CPU ADDRESS TO AGNUS MULTIPLEX ADDRESS FOR SDRAM ACCESS 
                  ADDED 1MB AND 2MB AGNUS OPTIONS
    29-JUL-2024 : ADDED SUPPORT FOR _DSACK TERMINATION.

GitHub: https://github.com/jasonsbeer/AmigaPCI
TO BUILD WITH APIO: apio build --top-module U712_TOP --fpga iCE40-HX4K-TQ144
*/

module U712_CHIPSET_RAM (

    input CLK7, CLK40, CLK80, nRESET, nRAS0, nRAS1, nCASL, nCASU, nRAMSPACE, nAWE, TT0, TT1, RnW, nTS, TA,
    input [20:1] A,

    output nDBEN, DBDIR, BANK0, BANK1, CAS_AGNUS,
    output reg DMA_CYCLE, BURST_CYCLE, nCRCS, nRAS, nCAS, nWE, CLKE, RAM_TA,
    output [9:0] DRA, 
    output reg [10:0] CMA

);

///////////////////////////
// SDRAM REFRESH COUNTER //
///////////////////////////

//WE USE THE 7MHz CLOCK TO DRIVE THE REFRESH COUNTER BECAUSE THAT 
//WILL ALWAYS BE AVAILABLE NO MATTER OUR CPU SPEED OR CONFIGURATION.
//SINCE WE ARE JUMPING BETWEEN CLOCK DOMAINS, WE NEED TO HAVE
//TWO PROCESSES TO ACCOMODATE THE JUMP.

localparam REFRESH_DEFAULT = 54;

wire REF_RESET;
reg REFRESH;
reg [5:0] REFRESH_COUNTER = 0; //6-BIT NUMBER MAX 63

assign REF_RESET = SDRAMCOM == ramstate_AUTOREFRESH;

always @(posedge CLK7 or posedge REF_RESET) begin
    if (REF_RESET) begin 
        REFRESH_COUNTER <= 0; 
    end else begin 
        REFRESH_COUNTER <= REFRESH_COUNTER + 1; 
    end
end

always @(negedge CLK80 or negedge nRESET) begin
    if (!nRESET) begin 
        REFRESH <= 0; 
    end else if (REFRESH_COUNTER >= REFRESH_DEFAULT) begin
        REFRESH <= 1;
    end else begin
        REFRESH <= 0;
    end
end

////////////////////////////////////
// AGNUS ROW AND COLUMN ADDRESSES //
////////////////////////////////////

//CAPTURE THE AGNUS ROW AND COLUMN ADDRESS WHEN RASx OR CASx IS ASSERTED.
//THIS IS TO FACILITATE DMA CYCLES.

//wire CAS_AGNUS;
wire DMA_RESET;
reg DMA_READY;
reg [9:0] DMA_ROW_ADDRESS;
reg [9:0] DMA_COL_ADDRESS;
//reg RAS_AGNUS;
wire RAS_AGNUS;
//reg [1:0] RAS0;
//reg [1:0] RAS1;

assign DMA_RESET = DMA_CYCLE || !nRESET;
assign CAS_AGNUS = !nCASL || !nCASU;
assign RAS_AGNUS = ((!nRAS0 && nRAS1) || (nRAS0 && !nRAS1));

/*always @(negedge CLK80, negedge nRESET) begin
    if (!nRESET) begin
        RAS_AGNUS <= 0;
        RAS0 <= 2'b11;
        RAS1 <= 2'b11;
    end else begin 
        RAS0 <= RAS0 << 1;
        RAS0[0] <= nRAS0;
        RAS1 <= RAS1 << 1;
        RAS1[0] <= nRAS1;
        if ((RAS0 == 2'b00 && RAS1 == 2'b11) || (RAS0 == 2'b11 && RAS1 == 2'b00)) begin	    
            RAS_AGNUS <= 1;	    
        end else begin
            RAS_AGNUS <= 0;
        end
    end
end*/
	
always @(posedge RAS_AGNUS, negedge nRESET) begin
    if (!nRESET) begin
        DMA_ROW_ADDRESS <= 10'b0000000000;
    end else begin
	    //DMA_ROW_ADDRESS <= DRA; //2MB Agnus
	    DMA_ROW_ADDRESS <= { nRAS0, DRA[8:0] }; //1MB Agnus
    end
end

always @(posedge CAS_AGNUS, negedge nRESET) begin
    if (!nRESET) begin
        DMA_COL_ADDRESS <= 10'b0000000000;
    end else begin
        DMA_COL_ADDRESS <= DRA;
    end
end

always @(posedge CAS_AGNUS, posedge DMA_RESET) begin
    if (DMA_RESET) begin
        DMA_READY <= 0;
    end else begin
        DMA_READY <= 1;
    end
end

///////////////////////
// CLK7 SYNCHRONIZER //
///////////////////////

reg [1:0] CLK7SYNC;

always @(negedge CLK80, negedge nRESET) begin
    if (!nRESET) begin
        CLK7SYNC <= 2'b00;
    end else begin
        CLK7SYNC <= { CLK7SYNC[0] , CLK7 };
    end
end

/////////////////////////
// CHIP RAM CONTROLLER //
/////////////////////////

//SDRAM IS USED TO IMPLEMENT THE CHIP RAM SPACE.

/*

THIS IS THE AGNUS DRAM MULTIPLEXING. 
MA9 ONLY EXISTS ON 8375 VARIANTS.
8372A USES A19 TO DRIVE RAS.

IN AGNUS 8372A, _RAS0 = A19. _RAS1 = A19 INVERSE.

     MA9 MA8 MA7 MA6 MA5 MA4 MA3 MA2 MA1 MA0
    ----------------------------------------
ROW: A19 A17 A16 A15 A14 A13 A12 A11 A10  A9
COL: A20 A18  A8  A7  A6  A5  A4  A3  A2  A1

*/

localparam [2:0] ramstate_NOP = 3'b000;
localparam [2:0] ramstate_PRECHARGE = 3'b001;
localparam [2:0] ramstate_MODEREGISTER = 3'b010;
localparam [2:0] ramstate_AUTOREFRESH = 3'b011;
localparam [2:0] ramstate_BANKACTIVATE = 3'b100;
localparam [2:0] ramstate_READ = 3'b101;
localparam [2:0] ramstate_WRITE = 3'b110;

reg [2:0] SDRAMCOM;
reg [7:0] RAM_COUNTER;
reg EMCLK_OUT;
reg RAM_CONFIGURED;
reg REFRESH_CYCLE;
reg RAM_CYCLE;
reg RnW_CYCLE;
reg TA_EN;
reg DBEN;
reg WAIT;

assign nDBEN = ~DBEN;
assign DBDIR = ~RnW_CYCLE;
assign BANK0 = 0;
assign BANK1 = 0;

//LATCH nTS
reg TS;
wire TS_RST;
assign TS_RST = !nRESET || RAM_CYCLE;

always @(posedge CLK40, posedge TS_RST) begin
    if (TS_RST) begin
        TS <= 0;
    end else if (!nTS && !nRAMSPACE) begin
        TS <= 1;
    end
end

//ASSERT THE SDRAM COMMANDS
reg CLK40_LAST;

always @(negedge CLK80, negedge nRESET) begin
    if (!nRESET) begin
        nCRCS <= 1;
        nRAS <= 1;
        nCAS <= 1;	
        nWE <= 1;
        CLKE <= 0;
        CMA <= 11'b00000000000;
        CLK40_LAST <= 1;
    end else begin

        CLKE <= EMCLK_OUT;
        CLK40_LAST <= CLK40;

        case (SDRAMCOM)

            ramstate_NOP:
                begin nCRCS <= 1; nRAS <= 1; nCAS <= 1; nWE <= 1; end

            ramstate_PRECHARGE:
                begin 
                    nCRCS <= 0; nRAS <= 0; nCAS <= 1; nWE <= 0;
                    CMA <= 11'b10000000000;                    
                end

            ramstate_MODEREGISTER :
                begin 
                    nCRCS <= 0; nRAS <= 0; nCAS <= 0;	nWE <= 0; 
                    CMA <= 11'b00000100010; 
                end

            ramstate_AUTOREFRESH :
                begin nCRCS <= 0; nRAS <= 0; nCAS <= 0;	nWE <= 1; end

            ramstate_BANKACTIVATE :
                begin 
                    nCRCS <= 0; nRAS <= 0; nCAS <= 1;	nWE <= 1; 

                    case (DMA_CYCLE)

                        1'b0 : CMA <= {1'b0, A[19], A[17:9]};
                        1'b1 : CMA <= {1'b0, DMA_ROW_ADDRESS[9:0]};

                    endcase

                end

            ramstate_READ :
                begin 
                    nCRCS <= 0; nRAS <= 1; nCAS <= 0;	nWE <= 1; 

                    case (DMA_CYCLE)

                        1'b0 : CMA <= {3'b000, A[18], A[8:2]}; //1MB CPU ACCESS
                        1'b1 : CMA <= {3'b00, DMA_COL_ADDRESS[9:1]};

                    endcase

                end

            ramstate_WRITE :
                begin 
                    nCRCS <= 0; nRAS <= 1; nCAS <= 0;	nWE <= 0; 

                    case (DMA_CYCLE)

                        1'b0 : CMA <= {3'b000, A[18], A[8:2]}; //1MB CPU ACCESS
                        1'b1 : CMA <= {3'b00, DMA_COL_ADDRESS[9:1]};

                    endcase
                    
                end

        endcase
    end
end

//SDRAM PROCESS

always @(posedge CLK80, negedge nRESET) begin
    if (!nRESET) begin
        SDRAMCOM = ramstate_NOP;
        EMCLK_OUT <= 0;
        RAM_COUNTER <= 8'h0;
        RAM_CONFIGURED <= 0;
        DMA_CYCLE <= 0;
        RAM_CYCLE <= 0;
        REFRESH_CYCLE <= 0;
        BURST_CYCLE <= 0;
        RnW_CYCLE <= 1;
        RAM_TA <= 0;
        DBEN <= 0;
        WAIT <= 0;
    end else begin

        //INCREMENT COUNTER DURING A CYCLE
        if (RAM_COUNTER != 8'h0 && !WAIT) begin RAM_COUNTER <= RAM_COUNTER + 1; end

        //CONFIGURE THE RAM AT STARTUP OR RESET
        if (!RAM_CONFIGURED) begin
            case (RAM_COUNTER)
                8'h0 : begin EMCLK_OUT <= 1; RAM_COUNTER <= 4'h1; end
                8'h1 : SDRAMCOM <= ramstate_PRECHARGE;
                8'h2 : SDRAMCOM <= ramstate_MODEREGISTER;
                8'h4, 4'h9 : SDRAMCOM <= ramstate_AUTOREFRESH;
                8'hD : begin RAM_CONFIGURED <= 1; RAM_COUNTER <= 4'h0; end
				default : SDRAMCOM <= ramstate_NOP;
            endcase

        //REFRESH CYCLE
        //WE DON'T INITIATE A REFRESH CYCLE WHEN A DMA CYCLE IS ABOUT TO BEGIN OR DURING AN ACTIVE RAM CYCLE.
        end else if ((!CAS_AGNUS && !RAM_CYCLE && !DMA_CYCLE && SDRAMCOM != ramstate_PRECHARGE && REFRESH) || REFRESH_CYCLE) begin
            case (RAM_COUNTER)
                8'h0 : begin RAM_COUNTER <= 4'h1; SDRAMCOM <= ramstate_AUTOREFRESH; REFRESH_CYCLE <= 1; end
                8'h1 : SDRAMCOM <= ramstate_NOP;
                8'h4 : begin RAM_COUNTER <= 4'h0; REFRESH_CYCLE <= 0; end
            endcase

        //RAM CYCLES
        end else if (!nRAMSPACE || DMA_READY || RAM_CYCLE || DMA_CYCLE) begin
            case (RAM_COUNTER)

                8'h00 : begin           

                    if (DMA_READY && SDRAMCOM != ramstate_PRECHARGE) begin //DMA CYCLE
                        //AGNUS ASSERTS THE _CASx SIGNALS IN STATE 5 SIGNIFYING A DMA CYCLE IS STARTING.
                        SDRAMCOM <= ramstate_BANKACTIVATE;
                        RAM_COUNTER <= 8'h01;
                        DMA_CYCLE <= 1; 
                        RAM_CYCLE <= 0;
                        BURST_CYCLE <= 0;
                        RnW_CYCLE <= nAWE;
                        DBEN <= DMA_COL_ADDRESS[0];                    
                    end else if (TS && !nRAMSPACE && !CLK40_LAST && !RAS_AGNUS && !CAS_AGNUS && SDRAMCOM != ramstate_PRECHARGE) begin //CPU CYCLE
                        //DON'T START A CPU RAM CYCLE IF AGNUS HAS ASSERTED ONE OF THE _RASx SIGNALS. THIS INDICATES A PENDING DMA CYCLE.
                        SDRAMCOM <= ramstate_BANKACTIVATE;
                        RAM_CYCLE <= 1; 
                        DMA_CYCLE <= 0;
                        RnW_CYCLE <= RnW;
                        DBEN <= 0;
                        if (TT0 && !TT1) begin
                            BURST_CYCLE <= 1;
                            //if ((RnW && !CLK40_LAST) || (!RnW && CLK40_LAST)) RAM_COUNTER <= 8'hA0;
                            RAM_COUNTER <= 8'hA0;
                        end else begin
                            RAM_COUNTER <= 8'h0A;
                        end
                    end else begin
                        DMA_CYCLE <= 0;
                        RAM_CYCLE <= 0;
                        BURST_CYCLE <= 0; 
                        DBEN <= 0;
                        SDRAMCOM <= ramstate_NOP;
                    end 

                end

                ////////////////
                // DMA STATES //
                ////////////////

                8'h01 : begin
                    SDRAMCOM <= ramstate_NOP;
                end

                8'h02 : begin
                    if (RnW_CYCLE) begin
                        SDRAMCOM <= ramstate_READ;
                    end else begin
                        SDRAMCOM <= ramstate_WRITE;
                    end	
                end

                8'h03 : 
                    begin
                        SDRAMCOM <= ramstate_PRECHARGE;
                        if (!RnW_CYCLE) begin                            
                            RAM_COUNTER <= 0; 
                        end
                    end

                8'h04 : 
                    begin
                        SDRAMCOM <= ramstate_NOP;
                        EMCLK_OUT <= 0;
                        WAIT <= 1; 
                    end

                8'h05 :
                begin
                    if (CLK7SYNC == 2'b10) begin
                        EMCLK_OUT <= 1;
                        DBEN <= 0;
                        WAIT <= 0;
                        RAM_COUNTER <= 0;
                    end 
                end

                ////////////////////////////
                // CPU (NON-BURST) STATES //
                ////////////////////////////

                8'h0A : begin
                    SDRAMCOM <= ramstate_NOP;
                end

                8'h0B : begin                    
                    if (RnW_CYCLE) begin
                        SDRAMCOM <= ramstate_READ;                        
                    end else begin
                        SDRAMCOM <= ramstate_WRITE;
                        RAM_TA <= 1;
                    end	
                end

                8'h0C : begin
                    SDRAMCOM <= ramstate_PRECHARGE;
                    if (RnW_CYCLE) begin 
                        EMCLK_OUT <= 0;
                    end
                end

                8'h0D : begin
                    SDRAMCOM <= ramstate_NOP;                    
                    if (RnW_CYCLE) begin
                        RAM_TA <= 1;
                    end else begin
                        RAM_TA <= 0;
                        RAM_COUNTER <= 0;
                    end
                end

                8'h0E : begin EMCLK_OUT <= 1; end

                8'h0F : 
                    begin 
                        RAM_COUNTER <= 0;
                        RAM_TA <= 0;
                    end

                //////////////////////
                // CPU BURST STATES //
                //////////////////////

                8'hA0 : begin
                    SDRAMCOM <= ramstate_NOP;
                end

                8'hA1 : begin

                    BURST_CYCLE <= ~RAS_AGNUS; //CANCEL BURST CYCLE WITH _TBI WHEN AGNUS INDICATES DMA CYCLE PENDING

                    //ASSERT _CAS AND _WE
                    if (RnW_CYCLE) begin
                        SDRAMCOM <= ramstate_READ;
                    end else begin
                        SDRAMCOM <= ramstate_WRITE;
                        if (!RAS_AGNUS) begin EMCLK_OUT <= 0; end //PROCEED WITH A BURST WRITE CYCLE.
                        RAM_TA <= 1;
                    end	
                end

                8'hA2 : 
                    begin

                        if (!BURST_CYCLE) begin
                            SDRAMCOM <= ramstate_PRECHARGE;
                        end else begin
                            SDRAMCOM <= ramstate_NOP;
                            if (RnW_CYCLE) begin EMCLK_OUT <= 1; end else begin EMCLK_OUT <= 0; end
                        end

                    end

                8'hA3 : 
                    begin                        

                        if (!BURST_CYCLE) begin

                            SDRAMCOM <= ramstate_NOP;

                            if (!RnW_CYCLE) begin 
                                RAM_COUNTER <= 0; //EARLY TERMINATION CPU BURST WRITE CYCLE
                                RAM_TA <= 0;
                            end else begin
                                RAM_TA <= 1;
                                EMCLK_OUT <= 0;
                            end

                        end else begin
                            RAM_TA <= 1;
                            if (RnW_CYCLE) begin EMCLK_OUT <= 0; end else begin EMCLK_OUT <= 1; end;
                        end

                    end

                8'hA4 : 
                
                    begin
                        if (BURST_CYCLE) begin 
                            if (RnW_CYCLE) begin 
                                EMCLK_OUT <= 1; 
                            end else begin
                                EMCLK_OUT <= 0; 
                            end
                        end
                    end

                8'hA5 : 
                    begin 
                         
                        if (!BURST_CYCLE) begin
                            RAM_COUNTER <= 0; //EARLY TERMINATION CPU BURST READ CYCLE
                            RAM_TA <= 0;
                            EMCLK_OUT <= 1;
                        end else begin
                            if (RnW_CYCLE) begin EMCLK_OUT <= 0; end else begin EMCLK_OUT <= 1; end;
                        end
                        
                    end

                8'hA6 : begin if (RnW_CYCLE) begin EMCLK_OUT <= 1; end else begin EMCLK_OUT <= 0; end; end

                8'hA7 : 
                    begin
                        if (RnW_CYCLE) begin 
                            EMCLK_OUT <= 0;
                        end else begin                            
                            RAM_TA <= 1; 
                            EMCLK_OUT <= 1;
                        end
                    end

                8'hA8 : 
                    begin                        
                        EMCLK_OUT <= 1;
                        if (!RnW_CYCLE) begin
                            RAM_TA <= 0;
                        end
                    end

                8'hA9 :
                    begin
                        if (!RnW_CYCLE) begin
                            SDRAMCOM <= ramstate_PRECHARGE; //END OF A BURST WRITE CYCLE
                            RAM_COUNTER <= 0;
                        end else begin
                            EMCLK_OUT <= 0;
                        end
                    end

                8'hAA : 
                    begin  
                        EMCLK_OUT <= 1;   
                    end

                8'hAB :
                    begin
                        RAM_TA <= 0;
                        RAM_COUNTER <= 0;
                        SDRAMCOM <= ramstate_PRECHARGE; //END OF A BURST READ CYCLE
                    end

            endcase
        end

    end
end  

endmodule
