jasonsbeer/AmigaPCI/Verilog/Daily/Verilog/U409/U409_ADDRESS_DECODE.v

/*
LICENSE:

This work is released under the Creative Commons Attribution-NonCommercial 4.0 International
https://creativecommons.org/licenses/by-nc/4.0/

You are free to:
Share — copy and redistribute the material in any medium or format
Adapt — remix, transform, and build upon the material
The licensor cannot revoke these freedoms as long as you follow the license terms.

Under the following terms:
Attribution — You must give appropriate credit , provide a link to the license, and indicate if changes were made . You may do so in any reasonable manner, but not in any way that suggests the licensor endorses you or your use.
NonCommercial — You may not use the material for commercial purposes .
No additional restrictions — You may not apply legal terms or technological measures that legally restrict others from doing anything the license permits.

RTL MODULE:

Engineer: Jason Neus
Design Name: U409
Module Name: U409_ADDRESS_DECODE
Project Name: AmigaPCI
Target Devices: iCE40-HX4K-TQ144

Description: ADDRESS DECODE

Date          Who  Description
-----------------------------------
01-JUL-2025   JN   INITIAL REV 6.0 CODE
15-OCT-2025   JN   Assert _ROMEN directly from address.
01-NOV-2025   JN   Roll back _ROMEN change above.
06-NOV-2025   JN   Fixed RTC address space.
11-NOV-2025   JN   Bridge base address fixed to $80000000
13-NOV-2025   JN   ATA address fixed to $DB0000

GitHub: https://github.com/jasonsbeer/AmigaPCI
*/

module U409_ADDRESS_DECODE
(

    //Clocks
    input CLK40, OVL, CIA_ENABLE, //CONFIGURED,
    
    //Cycle Start/Terminate
    input RESETn, RnW,
    input [1:0] TT,
    input [31:12] A,

    //Chip Selects
    input AUTOBOOT,
    output ROM_SPACE, CIA_SPACE, CIACS0n, CIACS1n, RAMSPACEn, REGSPACEn, AGNUS_SPACE,
    output AUTOVECTOR, RTC_SPACE, ATA_SPACE, ATA_ENn, // AUTOCONFIG_SPACE,
    output PCS0, PCS1, SCS0, SCS1, //BRIDGE_ENn,
    //output [1:0] PCIAT,

    //Base Addresses
    //input [7:1] LIDE_BASE,
    //input [3:0] PRO_BASE,    
    
    //FLASH
    input FLASH_DISJn,
    output FLASH_SPACE,
    output [1:0] FLASH_BANK

);

  ///////////////////////////
 // ZORRO 2 ADDRESS SPACE //
///////////////////////////

//WE NEED TO KNOW WHICH ADDRESS SPACE WE ARE IN SO WE DON'T RESPOND INCORRECTLY.

wire Z2_SPACE = RESETn && A[31:24] == 8'h00;

  ////////////////
 // ROM ENABLE //
////////////////

//ROM IS ENABLED AT THE RESET VECTOR $0000 0000 WHEN OVL IS ASSERTED (HIGH) AND AT $00F8 0000 - $00FF FFFF.
//KICKSTART JUMPS TO THE HIROM ADDRESS SPACE BEFORE OVL IS NEGATED, SO WE DON'T CHECK FOR IT AT THE HIROM ADDRESS.

assign ROM_SPACE  = Z2_SPACE && (LOWROM || HIROM);
wire   LOWROM  = A[23:19] == 5'b00000 && OVL;
wire   HIROM   = A[23:19] == 5'b11111;

  ///////////////////////
 // CIA ADDRESS SPACE //
///////////////////////

assign CIA_SPACE = Z2_SPACE && A[23:16] == 8'hBF;
assign CIACS0n = !(CIA_ENABLE && !A[12]);
assign CIACS1n = !(CIA_ENABLE && !A[13]);

  //////////////////
 // AGNUS SPACES //
//////////////////

//AGNUS CONTROLS ACCESS TO CHIPSET REGISTERS.
//REGISTERS ARE VISIBLE IN THE DATA SPACE.

assign RAMSPACEn   = !(Z2_SPACE && !OVL && A[23:21] == 3'b000);
assign REGSPACEn   = !(Z2_SPACE && A[23:16] == 8'hDF);
assign AGNUS_SPACE =  (!RAMSPACEn || !REGSPACEn);

  //////////////////////
 // AUTOVECTOR SPACE //
//////////////////////

//ALL INTERRUPT REQUESTS ARE SERVICED BY AUTOVECTORING.

assign AUTOVECTOR = RESETn && TT[1] && TT[0] && A[31:16] == 16'hFFFF;

  //////////////////////
 // AUTOCONFIG SPACE //
//////////////////////

//assign AUTOCONFIG_SPACE = Z2_SPACE && A[23:16] == 8'hE8;

  /////////////////////
 // REAL TIME CLOCK //
/////////////////////

//$00DC 0000 - $00DC FFFF
assign RTC_SPACE = Z2_SPACE && A[23:16] == 8'hDC;

  /////////
 // ATA //
/////////

//ATA ROM and chip selects.

//wire CS0 = !A[16] && !A[15] && !A[13] &&  A[12];
//wire CS1 = !A[16] && !A[15] &&  A[13] && !A[12];
wire CS0 = !A[15] && !A[13] &&  A[12];
wire CS1 = !A[15] &&  A[13] && !A[12];
assign PCS0 = !A[14] && CS0;
assign PCS1 =  A[14] && CS0;
assign SCS0 = !A[14] && CS1;
assign SCS1 =  A[14] && CS1;

//assign ATA_SPACE = Z2_SPACE && CONFIGURED && A[23:17] == LIDE_BASE; //128k
assign ATA_SPACE = Z2_SPACE && A[23:16] == 8'hDB;
assign ATA_ENn = !(ATA_SPACE && ATA_EN);

reg ATA_EN;
always @(posedge CLK40) begin
  if (!RESETn) begin
    ATA_EN <= 0;
  end else begin
    ATA_EN <= (ATA_SPACE && !RnW && AUTOBOOT) || ATA_EN;
  end
end

  //////////////////////
 // PCI BRIDGE SPACE //
//////////////////////

//The PCI bridge can be accessed in one of two ways.
//The first is the PCI Bridge registers in the Z2 space as a 64k device. These registers are defined by the PCI spec and support AUTOCONFIG cards.
//The second way is as a prometheus access in the Z3 space.
//The PCIAT (PCI Access Type) bus identifies the acess type for all bridge accesses.
//NOTE: The I/O space is basically deprectaed in the Rev 2.3 PCI spec, but is here for prometheus support. The PCI I/O space is not supported for AUTOCONFIG cards.

// Access Type         PCIAT1   PCIAT0
//-------------------------------------
//PCI Config Space 0     0        0
//PCI Config Space 1     0        1
//PCI Memory Space       1        0
//I/O Space              1        1

/*localparam [3:0] BRIDGE_BASE = 4'h8;

assign BRIDGE_ENn =  !(RESETn && A[31:29] == BRIDGE_BASE[3:1]);

wire PRO_CONF0_SPACE = A[27:20] == 8'hFC;
wire PRO_CONF1_SPACE = A[27:20] == 8'hFD;
wire PRO_IO_SPACE    = A[28:21] == 8'hFF;

assign PCIAT[1] = (PRO_IO_SPACE || (!PRO_IO_SPACE && !PRO_CONF0_SPACE && !PRO_CONF1_SPACE));
assign PCIAT[0] = (PRO_IO_SPACE || PRO_CONF1_SPACE);*/

  /////////////////
 // FLASH SPACE //
/////////////////

//The flash is 4 x 512k spaces, defined by the values of FBANK1 and FBANK0.
//The spaces are as follows...

// Amiga Address      FBANK1  FBANK0    FLASH Address
//-------------------------------------------------------
// $A80000 - $AFFFFF     0       0      $000000 - $07FFFF
// $B00000 - $B7FFFF     0       1      $080000 - $0FFFFF
// $E00000 - $E7FFFF     1       0      $100000 - $17FFFF
// $F00000 - $F7FFFF     1       1      $180000 - $1FFFFF

reg FLASH_DISABLE;
always @(posedge CLK40) begin
  if (!RESETn) begin
    FLASH_DISABLE <= 0;
  end else begin
    FLASH_DISABLE <= !FLASH_DISJn;
  end
end

wire ROM_SPACE_A = A[23:19] == 5'b10101; //A8-AF
wire ROM_SPACE_B = A[23:19] == 5'b10110; //B0-B7
wire ROM_SPACE_E = A[23:19] == 5'b11100; //E0-E7
wire ROM_SPACE_F = A[23:19] == 5'b11110; //F0-F7

assign FLASH_BANK[1] = A[22];
assign FLASH_BANK[0] = A[20];
assign FLASH_SPACE = Z2_SPACE && !FLASH_DISABLE && (ROM_SPACE_F || ROM_SPACE_E || ROM_SPACE_B || ROM_SPACE_A);
endmodule
